LtBrain/MuBook/hardware/v.1/BIOS.kicad_sch

## KiCad design hardware/v.1/BIOS.kicad_sch (2025-07-30)

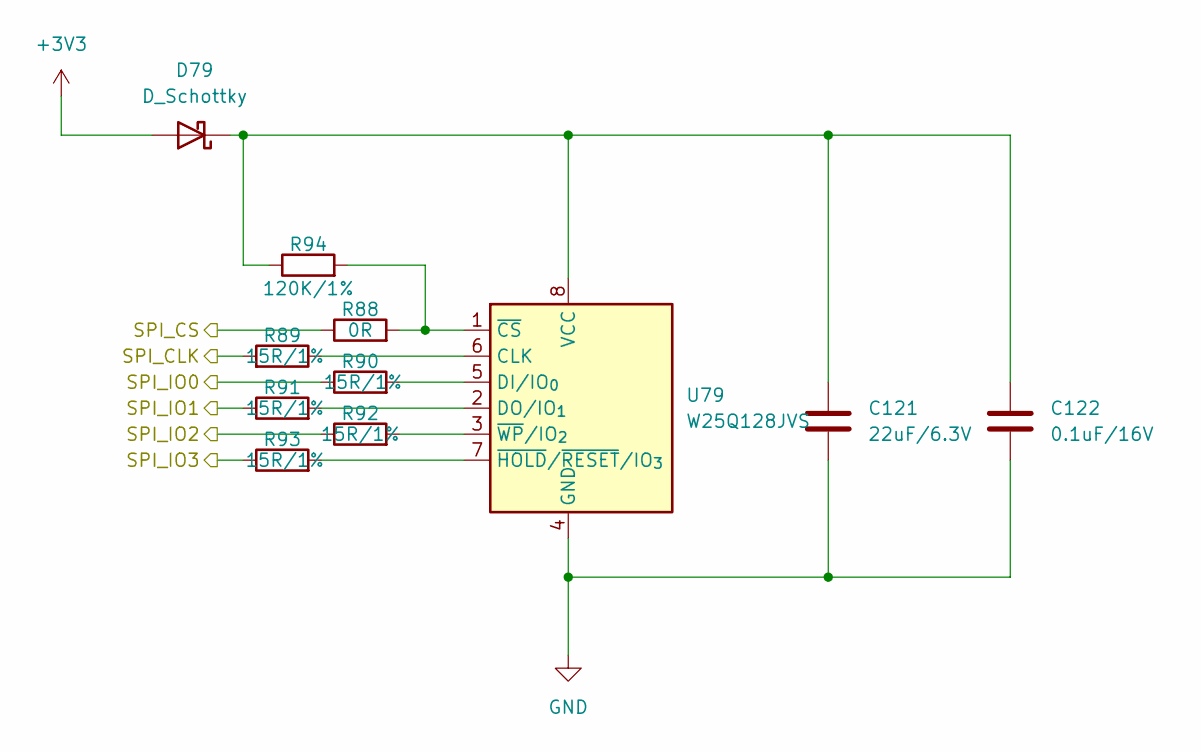
[picture p13: schematic BIOS.kicad_sch]

Parts:
C121: 22uF/6.3V; C_0402_1005Metric; Part# C105226; LCSC Part # C105226
C122: 0.1uF/16V; C_0402_1005Metric; Part# C83056; LCSC Part # C83056
D79: D_Schottky; D_SOD-923; Part# C239637; LCSC Part # C239637
R88: 0R; R_0402_1005Metric; Part# C325377; LCSC Part # C325377
R89, R90, R91, R92, R93: 15R/1%; R_0402_1005Metric; Part# C138052; LCSC Part # C138052
R94: 120K/1%; R_0402_1005Metric; Part# C93945; LCSC Part # C93945
U79: W25Q128JVS; SOIC-8_5.3x5.3mm_P1.27mm

Connections:
+3V3: D79.2 (A)
GND: C121.2, C122.2, U79.4 (GND)
unnamed: C121.1, C122.1, D79.1 (K), R94.1, U79.8 (VCC)
unnamed: R88.2, R94.2, U79.1 (~CS)
unnamed: R89.1, U79.6 (CLK)
unnamed: R90.2, U79.5 (DI/IO_{0})
unnamed: R91.2, U79.2 (DO/IO_{1})
unnamed: R92.2, U79.3 (~WP/IO_{2})
unnamed: R93.2, U79.7 (~HOLD/~RESET/IO_{3})
SPI_CLK: R89.2
SPI_CS: R88.1
SPI_IO0: R90.1
SPI_IO1: R91.1
SPI_IO2: R92.1
SPI_IO3: R93.1
