LtBrain/MuBook/hardware/v.1/GPIO.kicad_sch

## KiCad design hardware/v.1/GPIO.kicad_sch (2025-07-29)

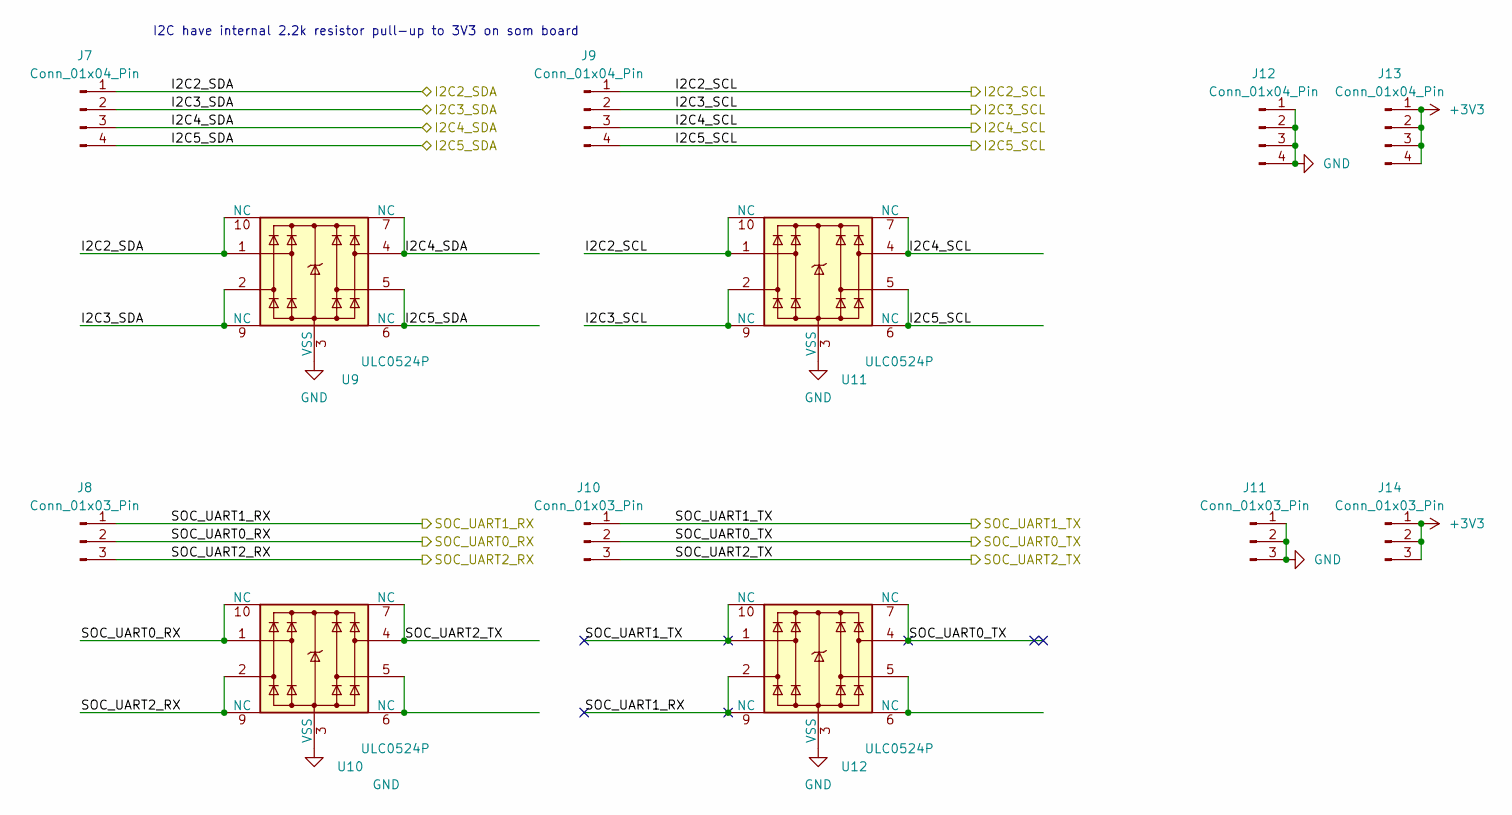
[picture p14: schematic GPIO.kicad_sch]

Parts:
J7, J9, J12, J13: Conn_01x04_Pin; PinHeader_1x04_P2.54mm_Vertical
J8, J10, J11, J14: Conn_01x03_Pin; PinHeader_1x03_P2.54mm_Vertical
U9, U10, U11, U12: ULC0524P; Diodes_UDFN-10_1.0x2.5mm_P0.5mm

Connections:
+3V3: J13.1, J13.2, J13.3, J13.4, J14.1, J14.2, J14.3
GND: J11.1, J11.2, J11.3, J12.1, J12.2, J12.3, J12.4, U9.3 (VSS), U9.8 (VSS), U10.3 (VSS), U10.8 (VSS), U11.3 (VSS), U11.8 (VSS), U12.3 (VSS), U12.8 (VSS)
I2C2_SCL: J9.1, U11.1, U11.10 (NC)
I2C2_SDA: J7.1, U9.1, U9.10 (NC)
I2C3_SCL: J9.2, U11.2, U11.9 (NC)
I2C3_SDA: J7.2, U9.2, U9.9 (NC)
I2C4_SCL: J9.3, U11.4, U11.7 (NC)
I2C4_SDA: J7.3, U9.4, U9.7 (NC)
I2C5_SCL: J9.4, U11.5, U11.6 (NC)
I2C5_SDA: J7.4, U9.5, U9.6 (NC)
unnamed: U10.5, U10.6 (NC)
unnamed: U12.5, U12.6 (NC)
SOC_UART0_RX: J8.2, U10.1, U10.10 (NC)
SOC_UART0_TX: J10.2, U12.4, U12.7 (NC)
SOC_UART1_RX: J8.1, U12.2, U12.9 (NC)
SOC_UART1_TX: J10.1, U12.1, U12.10 (NC)
SOC_UART2_RX: J8.3, U10.2, U10.9 (NC)
SOC_UART2_TX: J10.3, U10.4, U10.7 (NC)

Notes on the sheet:
I2C have internal 2.2k resistor pull-up to 3V3 on som board
