LtBrain/MuBook/hardware/v.1/Gigabit Ethernet.kicad_sch

## KiCad design hardware/v.1/Gigabit Ethernet.kicad_sch (2025-07-12)

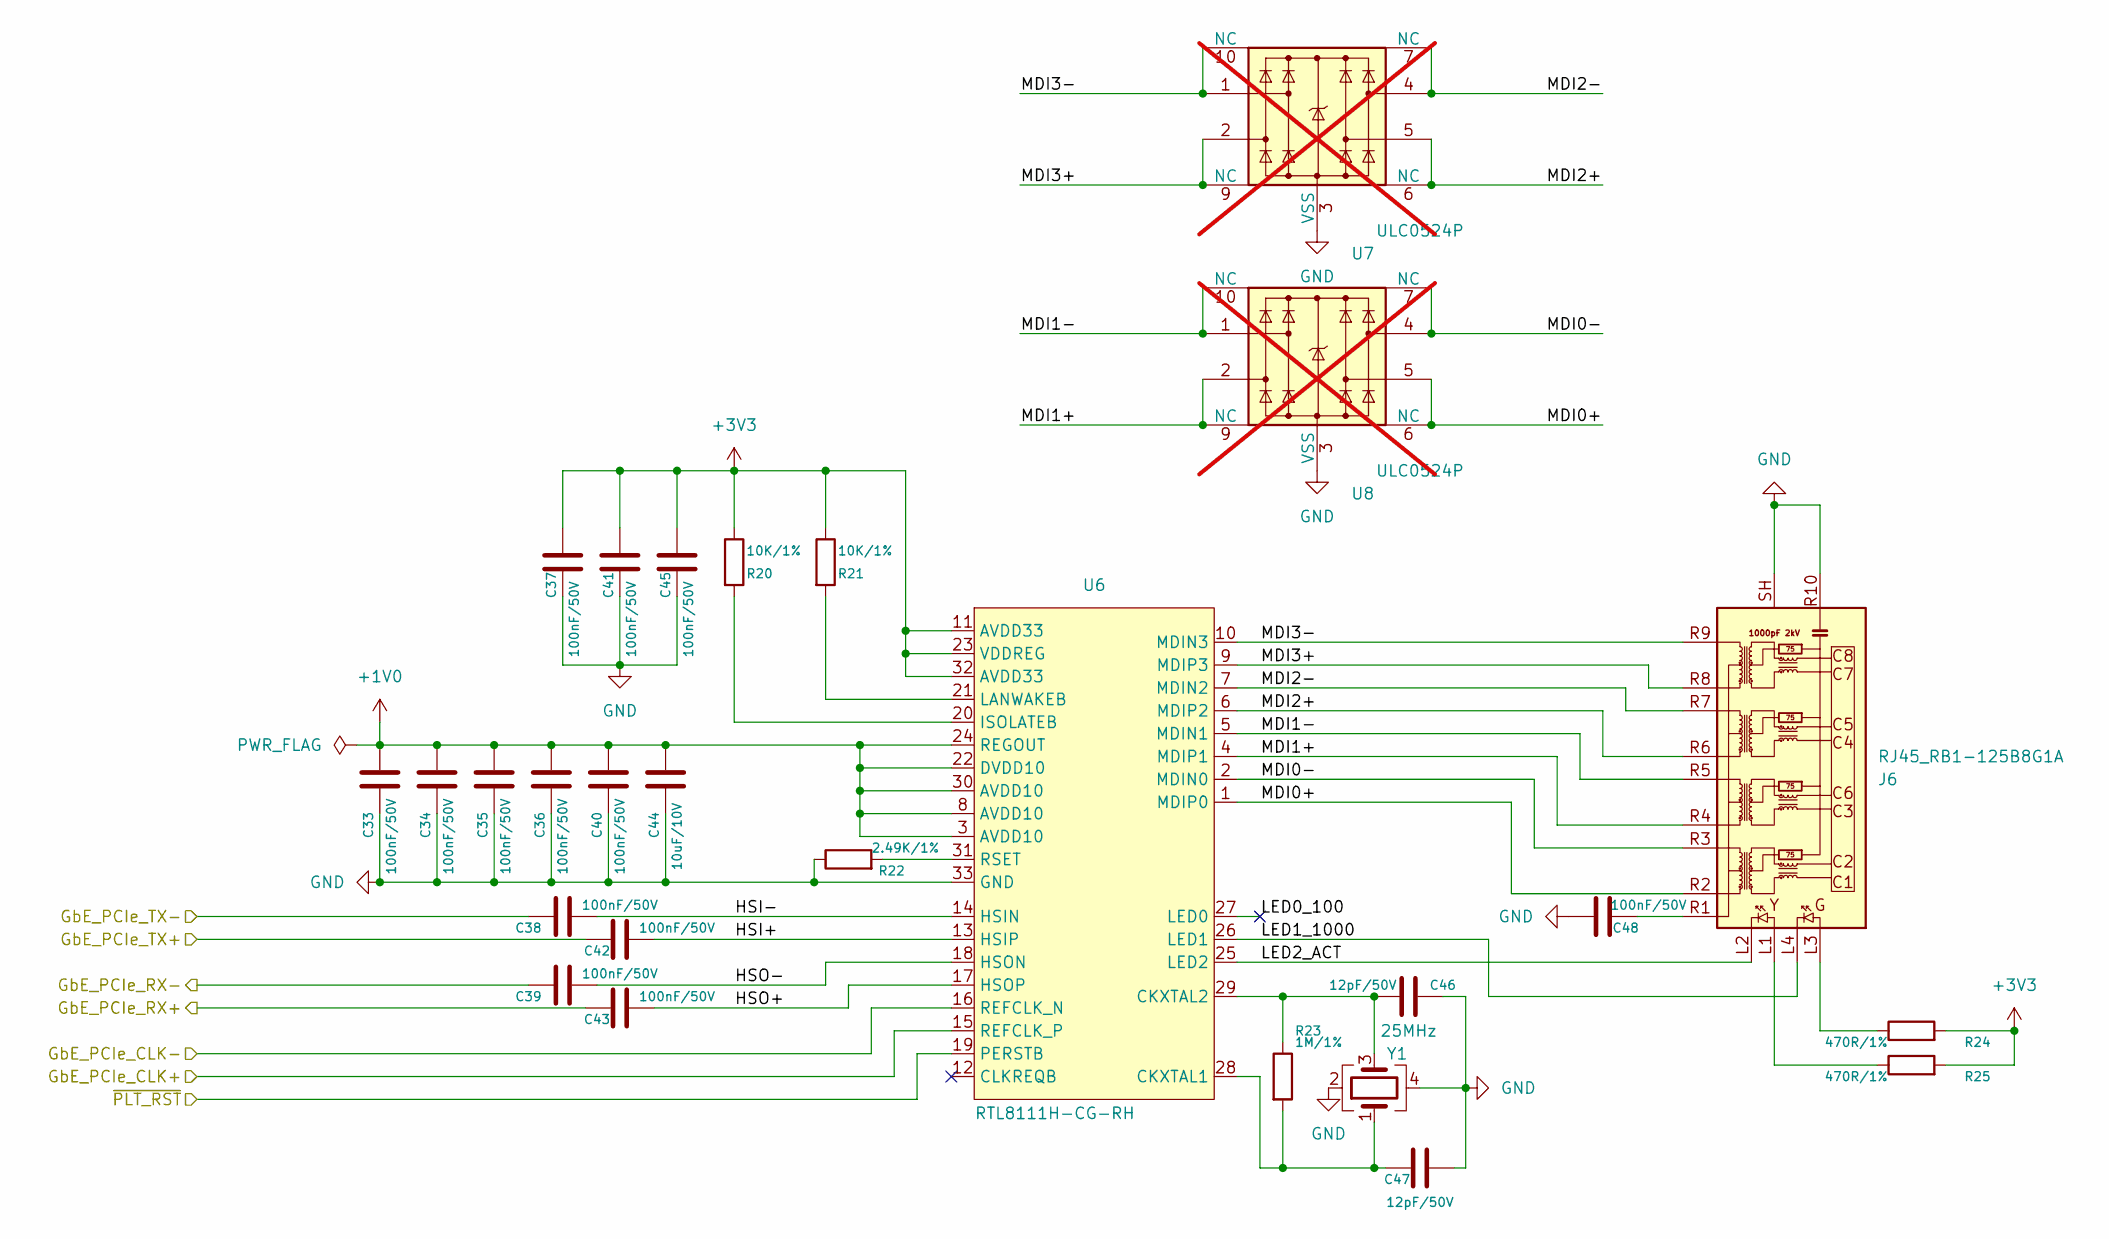
[picture p15: schematic Gigabit Ethernet.kicad_sch]

Parts:
C33, C34, C35, C36, C37, C38, C39, C40, C41, C42, C43, C45, C48: 100nF/50V; C_0402_1005Metric
C44: 10uF/10V; C_0402_1005Metric
C46, C47: 12pF/50V; C_0402_1005Metric
J6: RJ45_RB1-125B8G1A; RJ45_UDE_RB1-125B8G1A
R20, R21: 10K/1%; R_0402_1005Metric
R22: 2.49K/1%; R_0603_1608Metric
R23: 1M/1%; R_0402_1005Metric
R24, R25: 470R/1%; R_0402_1005Metric
U6: RTL8111H-CG-RH; QFN-32-1EP_4x4mm_P0.4mm_EP2.65x2.65mm
U7, U8: ULC0524P; Diodes_UDFN-10_1.0x2.5mm_P0.5mm; not fitted
Y1: 25MHz; Crystal_SMD_3225-4Pin_3.2x2.5mm

Connections:
+1V0: C33.2, C34.2, C35.2, C36.2, C40.2, C44.2, U6.3 (AVDD10), U6.8 (AVDD10), U6.22 (DVDD10), U6.24 (REGOUT), U6.30 (AVDD10)
+3V3: C37.2, C41.2, C45.2, R20.1, R21.1, R24.2, R25.2, U6.11 (AVDD33), U6.23 (VDDREG), U6.32 (AVDD33)
GND: C33.1, C34.1, C35.1, C36.1, C37.1, C40.1, C41.1, C44.1, C45.1, C46.1, C47.1, C48.2, J6.R10 (GND), J6.SH, R22.1, U6.33 (GND), U7.3 (VSS), U7.8 (VSS), U8.3 (VSS), U8.8 (VSS), Y1.2, Y1.4
GbE_PCIe_CLK+: U6.15 (REFCLK_P)
GbE_PCIe_CLK-: U6.16 (REFCLK_N)
GbE_PCIe_RX+: C43.2
GbE_PCIe_RX-: C39.2
GbE_PCIe_TX+: C42.2
GbE_PCIe_TX-: C38.2
HSI+: C42.1, U6.13 (HSIP)
HSI-: C38.1, U6.14 (HSIN)
HSO+: C43.1, U6.17 (HSOP)
HSO-: C39.1, U6.18 (HSON)
LED0_100: U6.27 (LED0)
LED1_1000: J6.L4, U6.26 (LED1)
LED2_ACT: J6.L2, U6.25 (LED2)
MDI0+: J6.R2 (TD1+), U6.1 (MDIP0), U8.5, U8.6 (NC)
MDI0-: J6.R3 (TD1-), U6.2 (MDIN0), U8.4, U8.7 (NC)
MDI1+: J6.R4 (TD2+), U6.4 (MDIP1), U8.2, U8.9 (NC)
MDI1-: J6.R5 (TD2-), U6.5 (MDIN1), U8.1, U8.10 (NC)
MDI2+: J6.R6 (TD3+), U6.6 (MDIP2), U7.5, U7.6 (NC)
MDI2-: J6.R7 (TD3-), U6.7 (MDIN2), U7.4, U7.7 (NC)
MDI3+: J6.R8 (TD4+), U6.9 (MDIP3), U7.2, U7.9 (NC)
MDI3-: J6.R9 (TD4-), U6.10 (MDIN3), U7.1, U7.10 (NC)
unnamed: C46.2, R23.1, U6.29 (CKXTAL2), Y1.3
unnamed: C47.2, R23.2, U6.28 (CKXTAL1), Y1.1
unnamed: C48.1, J6.R1 (CT)
unnamed: J6.L1, R25.1
unnamed: J6.L3, R24.1
unnamed: R20.2, U6.20 (ISOLATEB)
unnamed: R21.2, U6.21 (LANWAKEB)
unnamed: R22.2, U6.31 (RSET)
~PLT_RST: U6.19 (PERSTB)
