LtBrain/MuBook/hardware/v.1/HDMI.kicad_sch

## KiCad design hardware/v.1/HDMI.kicad_sch (2025-07-12)

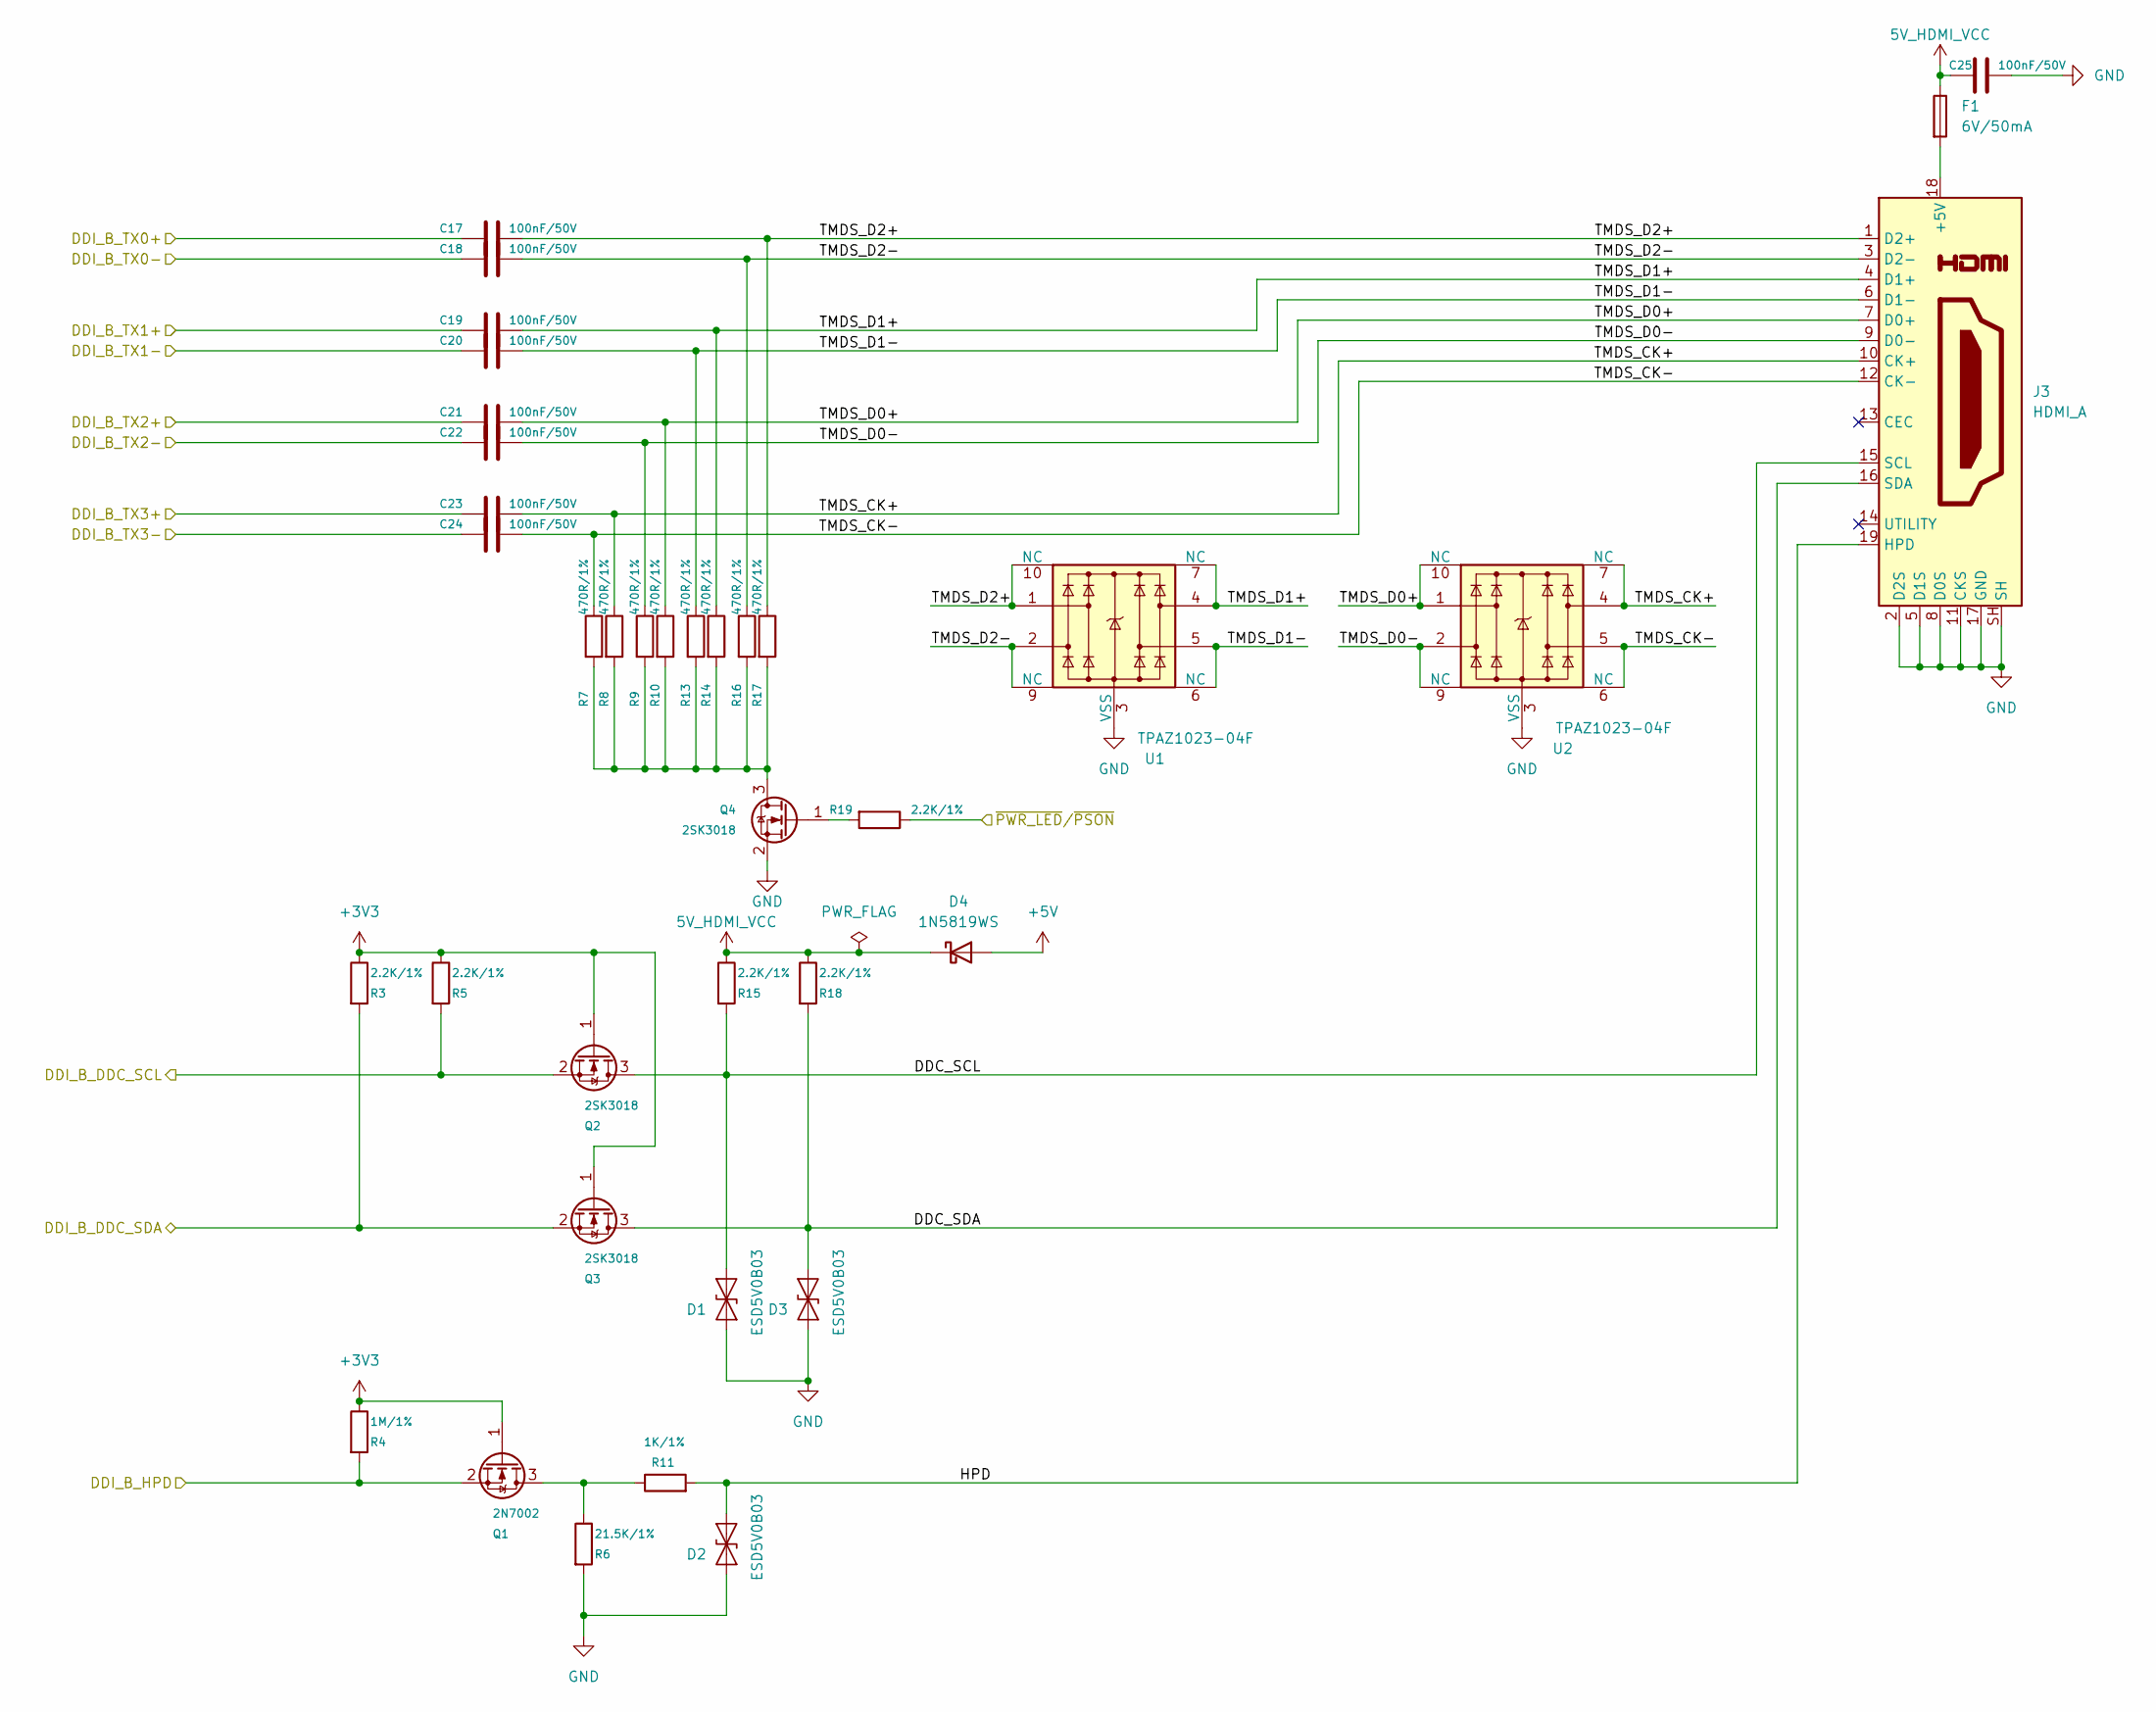
[picture p16: schematic HDMI.kicad_sch]

Parts:
C17, C18, C19, C20, C21, C22, C23, C24, C25: 100nF/50V; C_0402_1005Metric
D1, D2, D3: ESD5V0B03; D_0402_1005Metric
D4: 1N5819WS; D_SOD-323
F1: 6V/50mA; R_0603_1608Metric
J3: HDMI_A; HDMI_A_Molex_208658-1001_Horizontal
Q1: 2N7002; SOT-23
Q2, Q3, Q4: 2SK3018; SOT-23
R3, R5, R15, R18, R19: 2.2K/1%; R_0402_1005Metric
R4: 1M/1%; R_0402_1005Metric
R6: 21.5K/1%; R_0402_1005Metric
R7, R8, R9, R10, R13, R14, R16, R17: 470R/1%; R_0402_1005Metric
R11: 1K/1%; R_0402_1005Metric
U1, U2: TPAZ1023-04F; Diodes_UDFN-10_1.0x2.5mm_P0.5mm

Connections:
5V_HDMI_VCC: C25.1, D4.1 (K), F1.1, R15.1, R18.1
+3V3: Q1.1 (G), Q2.1 (G), Q3.1 (G), R3.1, R4.1, R5.1
+5V: D4.2 (A)
DDC_SCL: D1.2 (A2), J3.15 (SCL), Q2.3 (D), R15.2
DDC_SDA: D3.2 (A2), J3.16 (SDA), Q3.3 (D), R18.2
DDI_B_DDC_SCL: Q2.2 (S), R5.2
DDI_B_DDC_SDA: Q3.2 (S), R3.2
DDI_B_HPD: Q1.2 (S), R4.2
DDI_B_TX0+: C17.1
DDI_B_TX0-: C18.1
DDI_B_TX1+: C19.1
DDI_B_TX1-: C20.1
DDI_B_TX2+: C21.1
DDI_B_TX2-: C22.1
DDI_B_TX3+: C23.1
DDI_B_TX3-: C24.1
GND: C25.2, D1.1 (A1), D2.1 (A1), D3.1 (A1), J3.2 (D2S), J3.5 (D1S), J3.8 (D0S), J3.11 (CKS), J3.17 (GND), J3.SH, Q4.2 (S), R6.2, U1.3 (VSS), U1.8 (VSS), U2.3 (VSS), U2.8 (VSS)
HPD: D2.2 (A2), J3.19 (HPD), R11.2
unnamed: F1.2, J3.18 (+5V)
unnamed: Q1.3 (D), R6.1, R11.1
unnamed: Q4.1 (G), R19.2
unnamed: Q4.3 (D), R7.2, R8.2, R9.2, R10.2, R13.2, R14.2, R16.2, R17.2
TMDS_CK+: C23.2, J3.10 (CK+), R8.1, U2.4, U2.7 (NC)
TMDS_CK-: C24.2, J3.12 (CK-), R7.1, U2.5, U2.6 (NC)
TMDS_D0+: C21.2, J3.7 (D0+), R10.1, U2.1, U2.10 (NC)
TMDS_D0-: C22.2, J3.9 (D0-), R9.1, U2.2, U2.9 (NC)
TMDS_D1+: C19.2, J3.4 (D1+), R14.1, U1.4, U1.7 (NC)
TMDS_D1-: C20.2, J3.6 (D1-), R13.1, U1.5, U1.6 (NC)
TMDS_D2+: C17.2, J3.1 (D2+), R17.1, U1.1, U1.10 (NC)
TMDS_D2-: C18.2, J3.3 (D2-), R16.1, U1.2, U1.9 (NC)
~PWR_LED/~PSON: R19.1
