LtBrain/MuBook/hardware/v.1/LattePanda Module.kicad_sch

## KiCad design hardware/v.1/LattePanda Module.kicad_sch (2025-08-01)

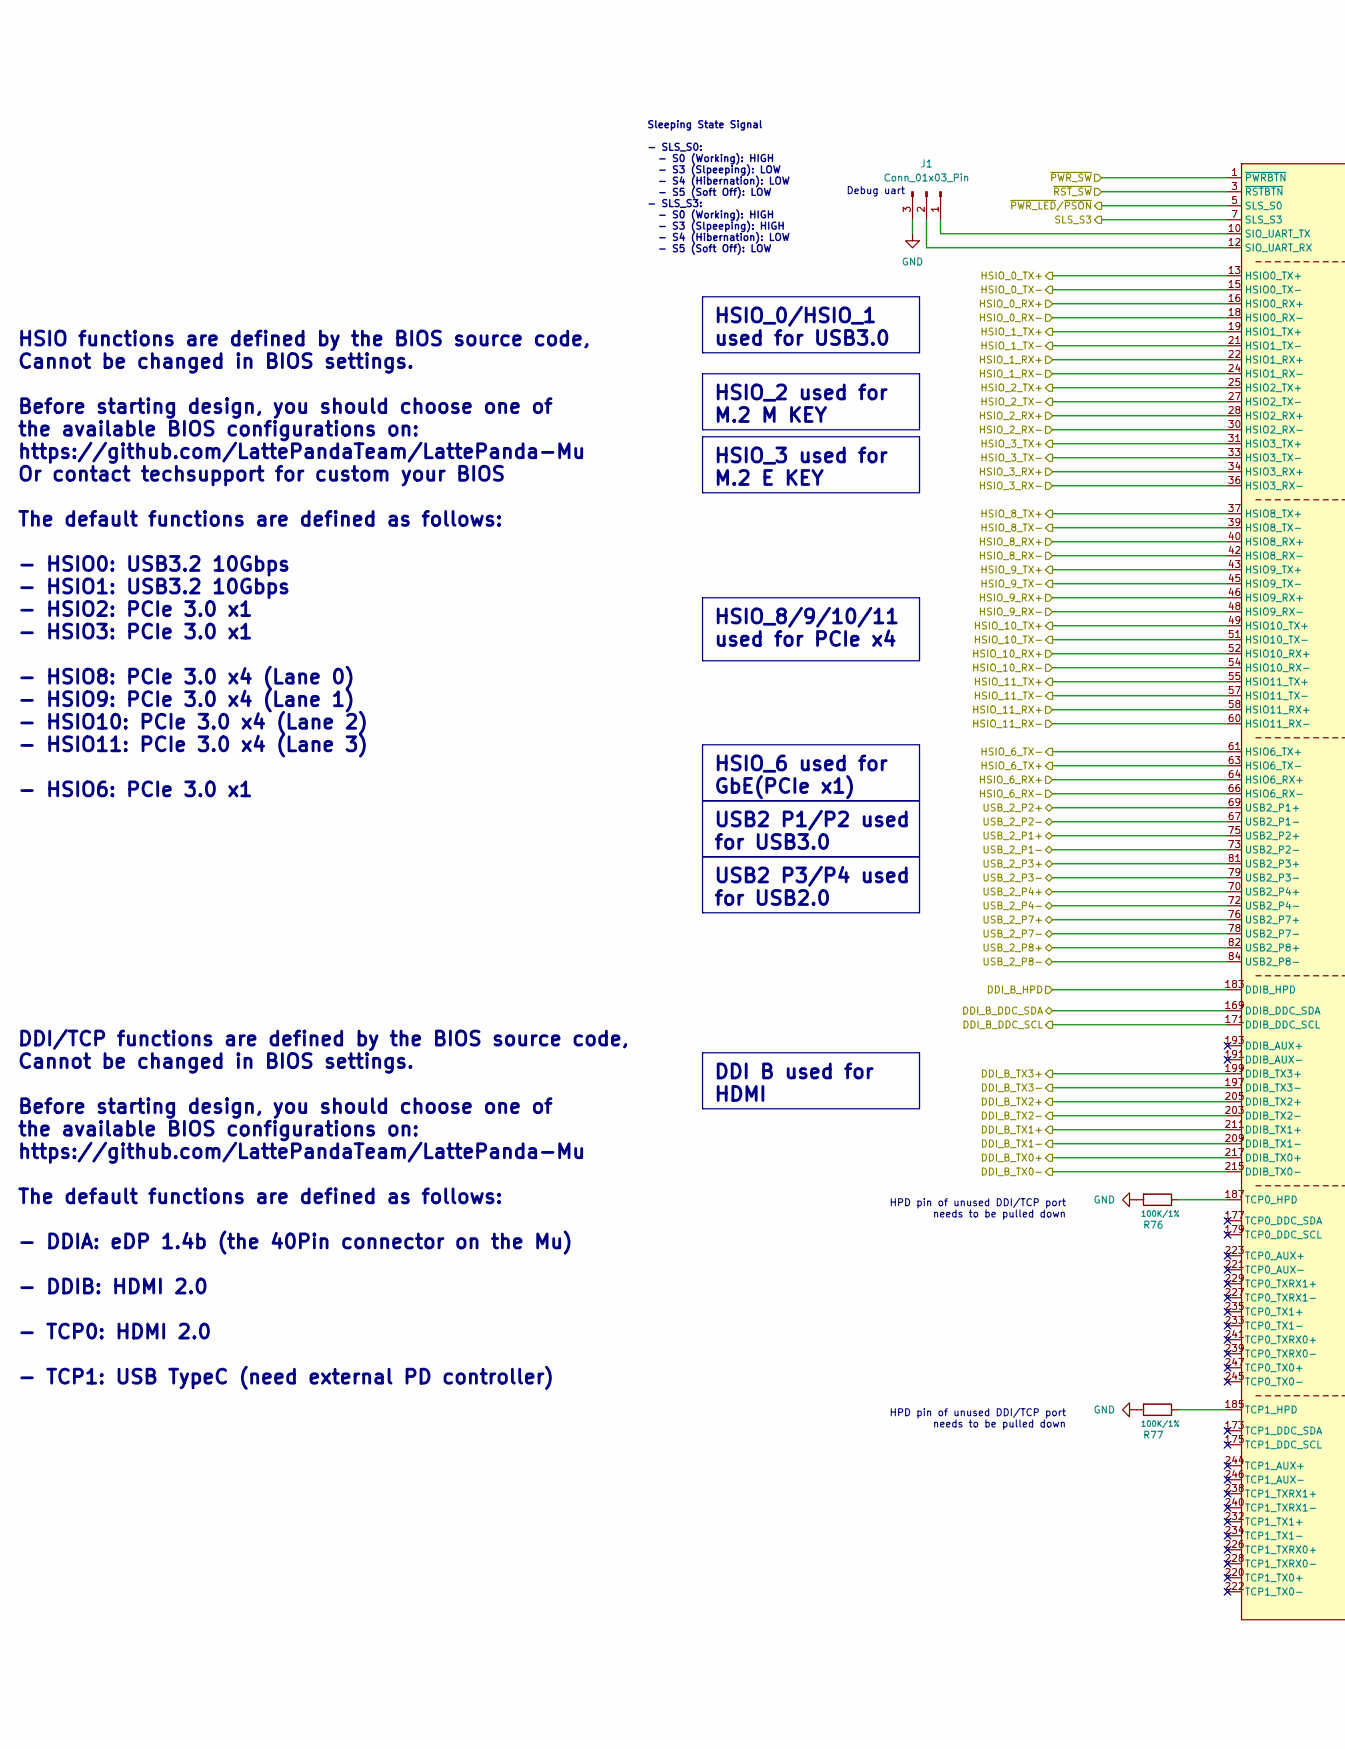
[picture p17: schematic LattePanda Module.kicad_sch, part in row 1, column 1]

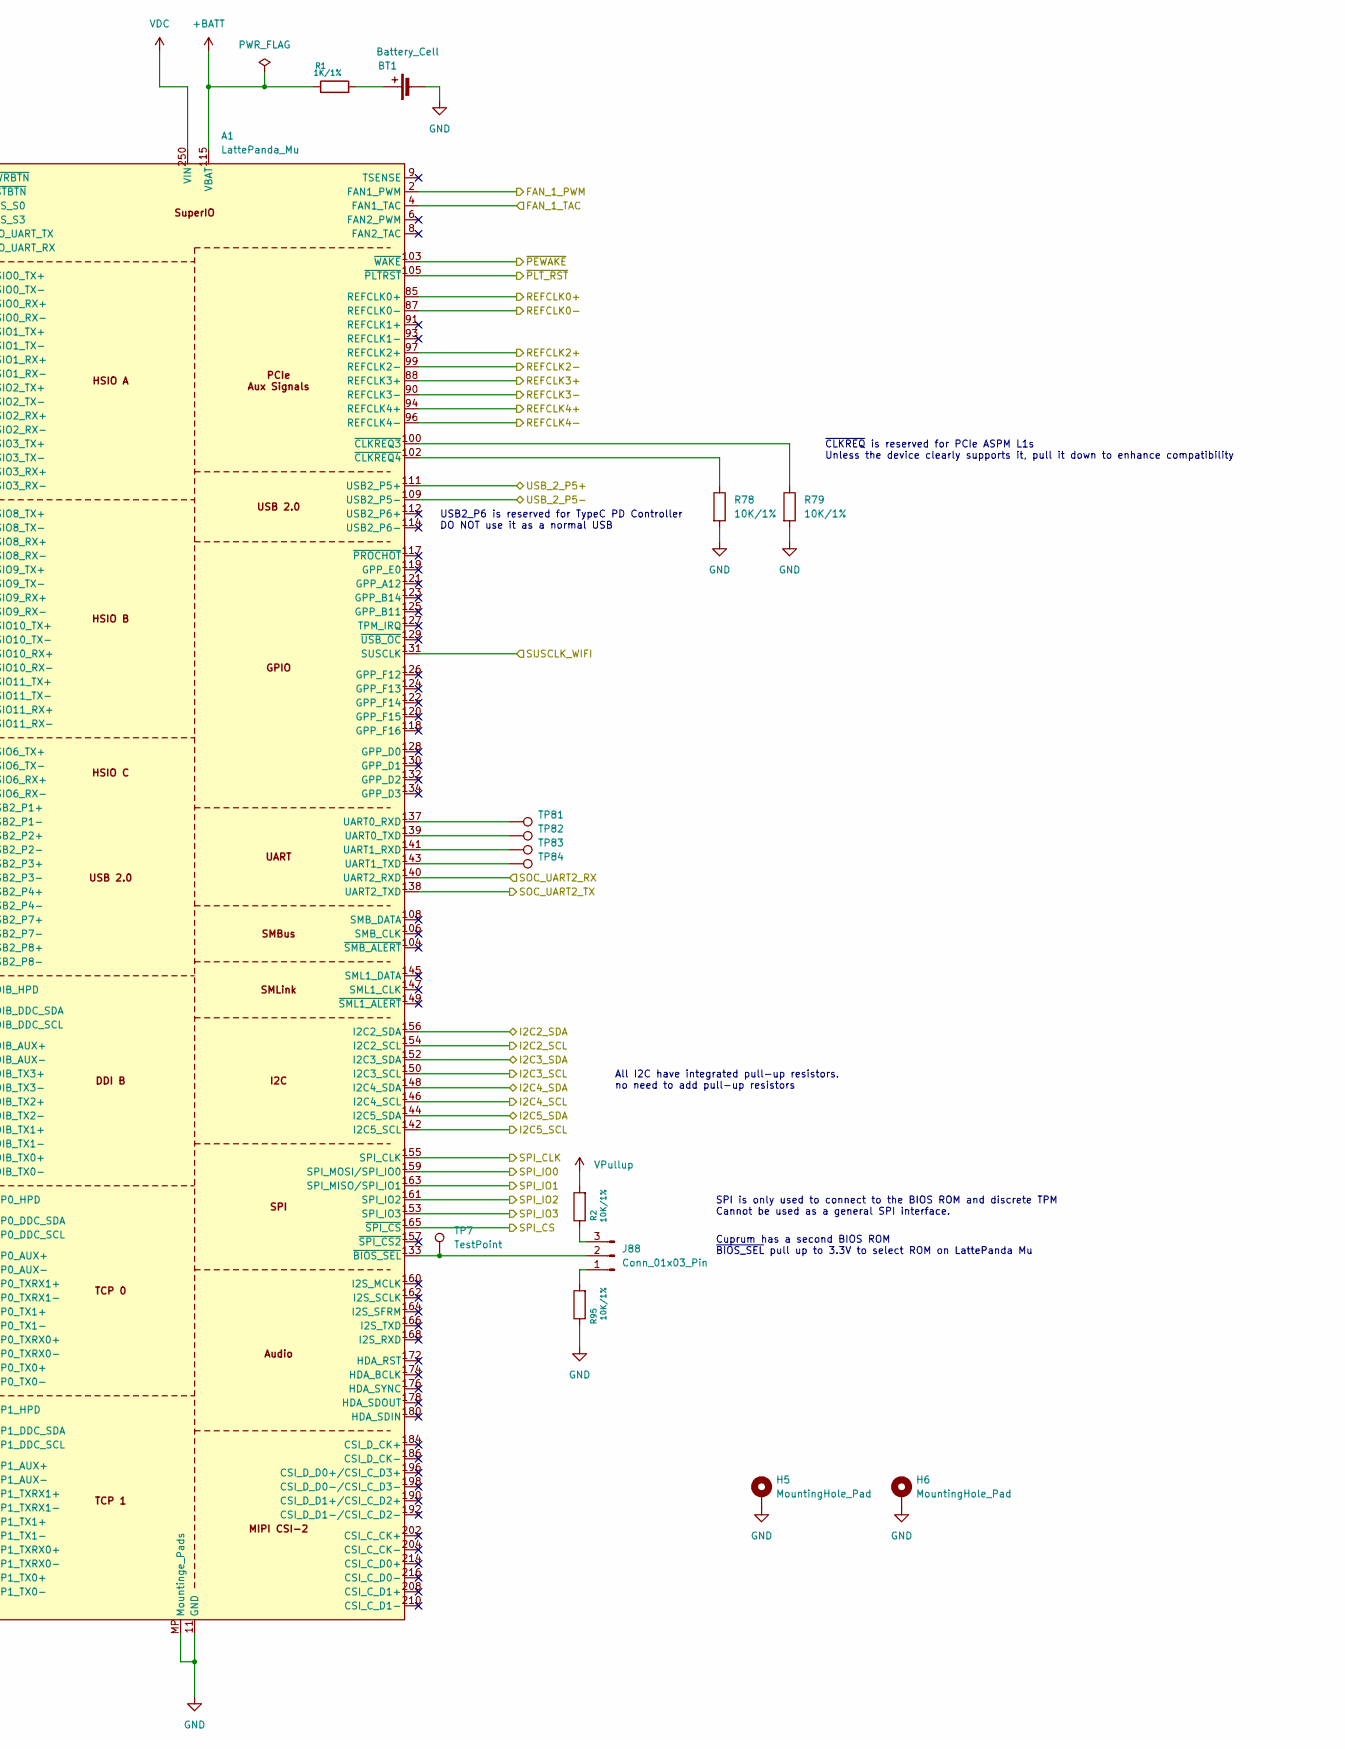
[picture p18: schematic LattePanda Module.kicad_sch, part in row 1, column 2]

Parts:
A1: LattePanda_Mu; LattePanda_Module_H8.0mm_Horizontal
BT1: Battery_Cell; Battery_Holder_CR1220_S8411-45R
H5, H6: MountingHole_Pad; MountingHole_2.2mm_M2_DIN965_Pad
J1: Conn_01x03_Pin; PinHeader_1x03_P2.54mm_Vertical
J88: Conn_01x03_Pin; PinHeader_1x03_P2.54mm_Vertical; MPN PZ2.54-1*3
R1: 1K/1%; R_0402_1005Metric
R2, R95: 10K/1%; R_0402_1005Metric; Part# C60490; LCSC Part # C60490
R76, R77: 100K/1%; R_0402_1005Metric
R78, R79: 10K/1%; R_0402_1005Metric
TP7: TestPoint; TestPoint_Pad_D1.5mm
TP81, TP82, TP83, TP84: TestPoint; TestPoint_Pad_D1.0mm

Connections:
+BATT: A1.115 (VBAT), R1.1
DDI_B_DDC_SCL: A1.171 (DDIB_DDC_SCL)
DDI_B_DDC_SDA: A1.169 (DDIB_DDC_SDA)
DDI_B_HPD: A1.183 (DDIB_HPD)
DDI_B_TX0+: A1.217 (DDIB_TX0+)
DDI_B_TX0-: A1.215 (DDIB_TX0-)
DDI_B_TX1+: A1.211 (DDIB_TX1+)
DDI_B_TX1-: A1.209 (DDIB_TX1-)
DDI_B_TX2+: A1.205 (DDIB_TX2+)
DDI_B_TX2-: A1.203 (DDIB_TX2-)
DDI_B_TX3+: A1.199 (DDIB_TX3+)
DDI_B_TX3-: A1.197 (DDIB_TX3-)
FAN_1_PWM: A1.2 (FAN1_PWM)
FAN_1_TAC: A1.4 (FAN1_TAC)
GND: A1.11 (GND), A1.14 (GND), A1.17 (GND), A1.20 (GND), A1.23 (GND), A1.26 (GND), A1.29 (GND), A1.32 (GND), A1.35 (GND), A1.38 (GND), A1.41 (GND), A1.44 (GND), A1.47 (GND), A1.50 (GND), A1.53 (GND), A1.56 (GND), A1.59 (GND), A1.62 (GND), A1.65 (GND), A1.68 (GND), A1.71 (GND), A1.74 (GND), A1.77 (GND), A1.80 (GND), A1.83 (GND), A1.86 (GND), A1.89 (GND), A1.92 (GND), A1.95 (GND), A1.98 (GND), A1.101 (GND), A1.107 (GND), A1.110 (GND), A1.113 (GND), A1.116 (GND), A1.135 (GND), A1.136 (GND), A1.151 (GND), A1.158 (GND), A1.167 (GND), A1.170 (GND), A1.181 (GND), A1.182 (GND), A1.188 (GND), A1.189 (GND), A1.194 (GND), A1.195 (GND), A1.200 (GND), A1.201 (GND), A1.206 (GND), A1.207 (GND), A1.212 (GND), A1.213 (GND), A1.218 (GND), A1.219 (GND), A1.224 (GND), A1.225 (GND), A1.230 (GND), A1.231 (GND), A1.236 (GND), A1.237 (GND), A1.242 (GND), A1.243 (GND), A1.248 (GND), A1.249 (GND), A1.MP (Mountinge_Pads), BT1.2 (-), H5.1, H6.1, J1.3, R76.2, R77.2, R78.2, R79.2, R95.1
HSIO_0_RX+: A1.16 (HSIO0_RX+)
HSIO_0_RX-: A1.18 (HSIO0_RX-)
HSIO_0_TX+: A1.13 (HSIO0_TX+)
HSIO_0_TX-: A1.15 (HSIO0_TX-)
HSIO_1_RX+: A1.22 (HSIO1_RX+)
HSIO_1_RX-: A1.24 (HSIO1_RX-)
HSIO_1_TX+: A1.19 (HSIO1_TX+)
HSIO_1_TX-: A1.21 (HSIO1_TX-)
HSIO_2_RX+: A1.28 (HSIO2_RX+)
HSIO_2_RX-: A1.30 (HSIO2_RX-)
HSIO_2_TX+: A1.25 (HSIO2_TX+)
HSIO_2_TX-: A1.27 (HSIO2_TX-)
HSIO_3_RX+: A1.34 (HSIO3_RX+)
HSIO_3_RX-: A1.36 (HSIO3_RX-)
HSIO_3_TX+: A1.31 (HSIO3_TX+)
HSIO_3_TX-: A1.33 (HSIO3_TX-)
HSIO_6_RX+: A1.64 (HSIO6_RX+)
HSIO_6_RX-: A1.66 (HSIO6_RX-)
HSIO_6_TX+: A1.63 (HSIO6_TX-)
HSIO_6_TX-: A1.61 (HSIO6_TX+)
HSIO_8_RX+: A1.40 (HSIO8_RX+)
HSIO_8_RX-: A1.42 (HSIO8_RX-)
HSIO_8_TX+: A1.37 (HSIO8_TX+)
HSIO_8_TX-: A1.39 (HSIO8_TX-)
HSIO_9_RX+: A1.46 (HSIO9_RX+)
HSIO_9_RX-: A1.48 (HSIO9_RX-)
HSIO_9_TX+: A1.43 (HSIO9_TX+)
HSIO_9_TX-: A1.45 (HSIO9_TX-)
HSIO_10_RX+: A1.52 (HSIO10_RX+)
HSIO_10_RX-: A1.54 (HSIO10_RX-)
HSIO_10_TX+: A1.49 (HSIO10_TX+)
HSIO_10_TX-: A1.51 (HSIO10_TX-)
HSIO_11_RX+: A1.58 (HSIO11_RX+)
HSIO_11_RX-: A1.60 (HSIO11_RX-)
HSIO_11_TX+: A1.55 (HSIO11_TX+)
HSIO_11_TX-: A1.57 (HSIO11_TX-)
I2C2_SCL: A1.154 (I2C2_SCL)
I2C2_SDA: A1.156 (I2C2_SDA)
I2C3_SCL: A1.150 (I2C3_SCL)
I2C3_SDA: A1.152 (I2C3_SDA)
I2C4_SCL: A1.146 (I2C4_SCL)
I2C4_SDA: A1.148 (I2C4_SDA)
I2C5_SCL: A1.142 (I2C5_SCL)
I2C5_SDA: A1.144 (I2C5_SDA)
unnamed: A1.10 (SIO_UART_TX), J1.1
unnamed: A1.12 (SIO_UART_RX), J1.2
unnamed: A1.100 (~CLKREQ3), R79.1
unnamed: A1.102 (~CLKREQ4), R78.1
unnamed: A1.133 (~BIOS_SEL), J88.2, TP7.1
unnamed: A1.137 (UART0_RXD), TP81.1
unnamed: A1.139 (UART0_TXD), TP82.1
unnamed: A1.141 (UART1_RXD), TP83.1
unnamed: A1.143 (UART1_TXD), TP84.1
unnamed: A1.185 (TCP1_HPD), R77.1
unnamed: A1.187 (TCP0_HPD), R76.1
unnamed: BT1.1 (+), R1.2
unnamed: J88.1, R95.2
unnamed: J88.3, R2.1
REFCLK0+: A1.85 (REFCLK0+)
REFCLK0-: A1.87 (REFCLK0-)
REFCLK2+: A1.97 (REFCLK2+)
REFCLK2-: A1.99 (REFCLK2-)
REFCLK3+: A1.88 (REFCLK3+)
REFCLK3-: A1.90 (REFCLK3-)
REFCLK4+: A1.94 (REFCLK4+)
REFCLK4-: A1.96 (REFCLK4-)
SLS_S3: A1.7 (SLS_S3)
SOC_UART2_RX: A1.140 (UART2_RXD)
SOC_UART2_TX: A1.138 (UART2_TXD)
SPI_CLK: A1.155 (SPI_CLK)
SPI_CS: A1.165 (~SPI_CS)
SPI_IO0: A1.159 (SPI_MOSI/SPI_IO0)
SPI_IO1: A1.163 (SPI_MISO/SPI_IO1)
SPI_IO2: A1.161 (SPI_IO2)
SPI_IO3: A1.153 (SPI_IO3)
SUSCLK_WIFI: A1.131 (SUSCLK)
USB_2_P1+: A1.75 (USB2_P2+)
USB_2_P1-: A1.73 (USB2_P2-)
USB_2_P2+: A1.69 (USB2_P1+)
USB_2_P2-: A1.67 (USB2_P1-)
USB_2_P3+: A1.81 (USB2_P3+)
USB_2_P3-: A1.79 (USB2_P3-)
USB_2_P4+: A1.70 (USB2_P4+)
USB_2_P4-: A1.72 (USB2_P4-)
USB_2_P5+: A1.111 (USB2_P5+)
USB_2_P5-: A1.109 (USB2_P5-)
USB_2_P7+: A1.76 (USB2_P7+)
USB_2_P7-: A1.78 (USB2_P7-)
USB_2_P8+: A1.82 (USB2_P8+)
USB_2_P8-: A1.84 (USB2_P8-)
VDC: A1.250 (VIN), A1.251 (VIN), A1.252 (VIN), A1.253 (VIN), A1.254 (VIN), A1.255 (VIN), A1.256 (VIN), A1.257 (VIN), A1.258 (VIN), A1.259 (VIN), A1.260 (VIN)
VPullup: R2.2
~PEWAKE: A1.103 (~WAKE)
~PLT_RST: A1.105 (~PLTRST)
~PWR_LED/~PSON: A1.5 (SLS_S0)
~PWR_SW: A1.1 (~PWRBTN)
~RST_SW: A1.3 (~RSTBTN)

Notes on the sheet:
HSIO functions are defined by the BIOS source code, Cannot be changed in BIOS settings. Before starting design, you should choose one of the available BIOS configurations on: https://github.com/LattePandaTeam/LattePanda-Mu Or contact techsupport for custom your BIOS The default functions are define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
HPD pin of unused DDI/TCP port needs to be pulled down
Cuprum has a second BIOS ROM ~{BIOS_SEL} pull up to 3.3V to select ROM on LattePanda Mu
DDI/TCP functions are defined by the BIOS source code, Cannot be changed in BIOS settings. Before starting design, you should choose one of the available BIOS configurations on: https://github.com/LattePandaTeam/LattePanda-Mu The default functions are defined as follows: - DDIA: eDP 1.4b (the 40Pin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
Sleeping State Signal - SLS_S0: - S0 (Working): HIGH - S3 (Slpeeping): LOW - S4 (Hibernation): LOW - S5 (Soft Off): LOW - SLS_S3: - S0 (Working): HIGH - S3 (Slpeeping): HIGH - S4 (Hibernation): LOW - S5 (Soft Off): LOW
USB2_P6 is reserved for TypeC PD Controller DO NOT use it as a normal USB
SPI is only used to connect to the BIOS ROM and discrete TPM Cannot be used as a general SPI interface.
All I2C have integrated pull-up resistors. no need to add pull-up resistors
Debug uart
~{CLKREQ} is reserved for PCIe ASPM L1s Unless the device clearly supports it, pull it down to enhance compatibility
HSIO_0/HSIO_1 used for USB3.0
HSIO_2 used for M.2 M KEY
HSIO_6 used for GbE(PCIe x1)
USB2 P3/P4 used for USB2.0
DDI B used for HDMI
HSIO_3 used for M.2 E KEY
HSIO_8/9/10/11 used for PCIe x4
USB2 P1/P2 used for USB3.0
