LtBrain/MuBook/hardware/v.1/M.2 E&M Key.kicad_sch

## KiCad design hardware/v.1/M.2 E&M Key.kicad_sch (2025-07-12)

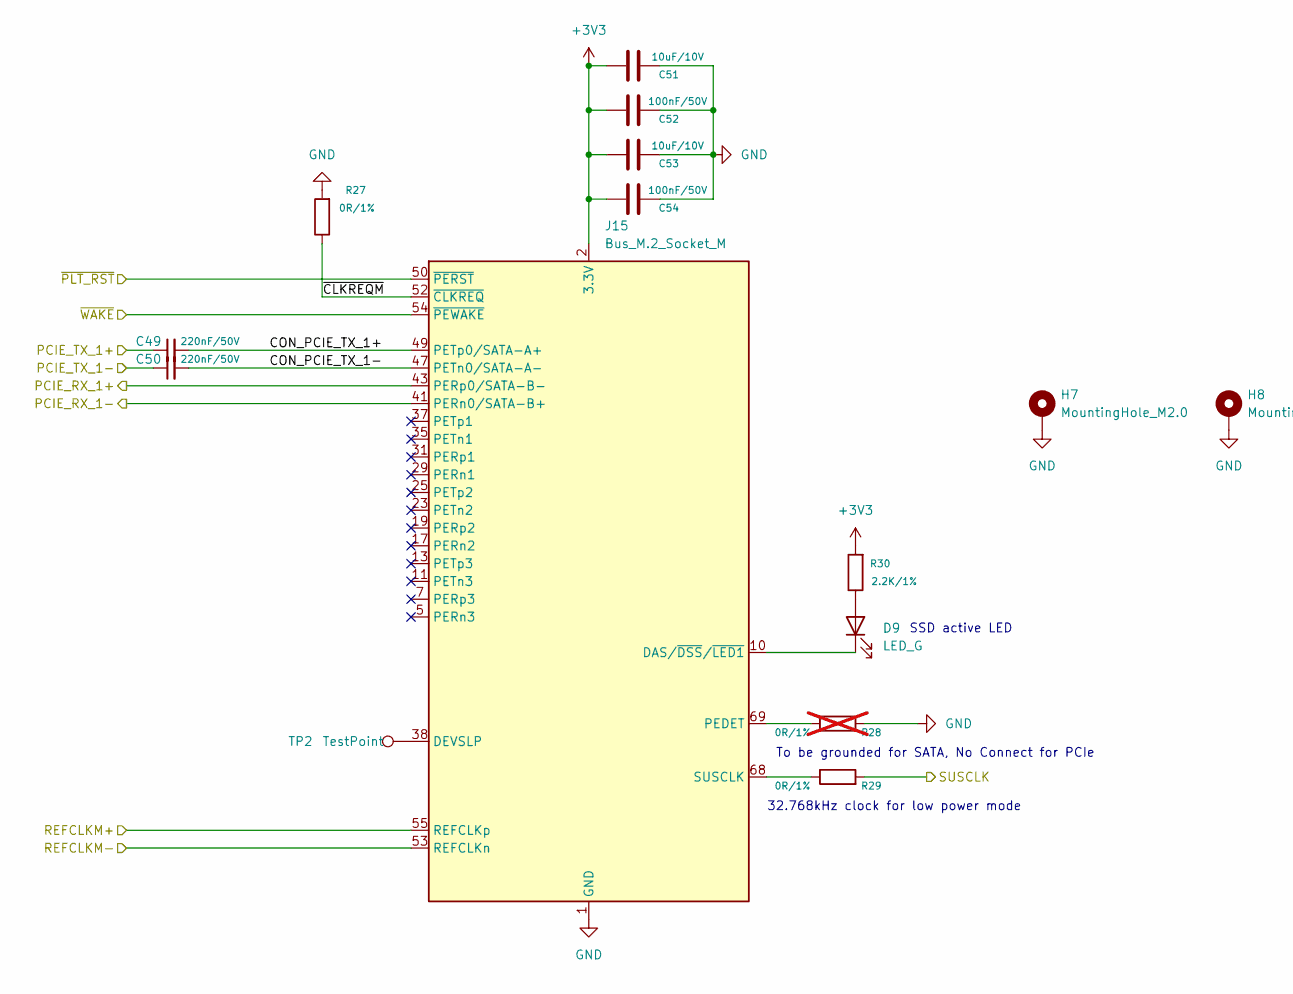
[picture p19: schematic M.2 E&M Key.kicad_sch, part in row 1, column 1]

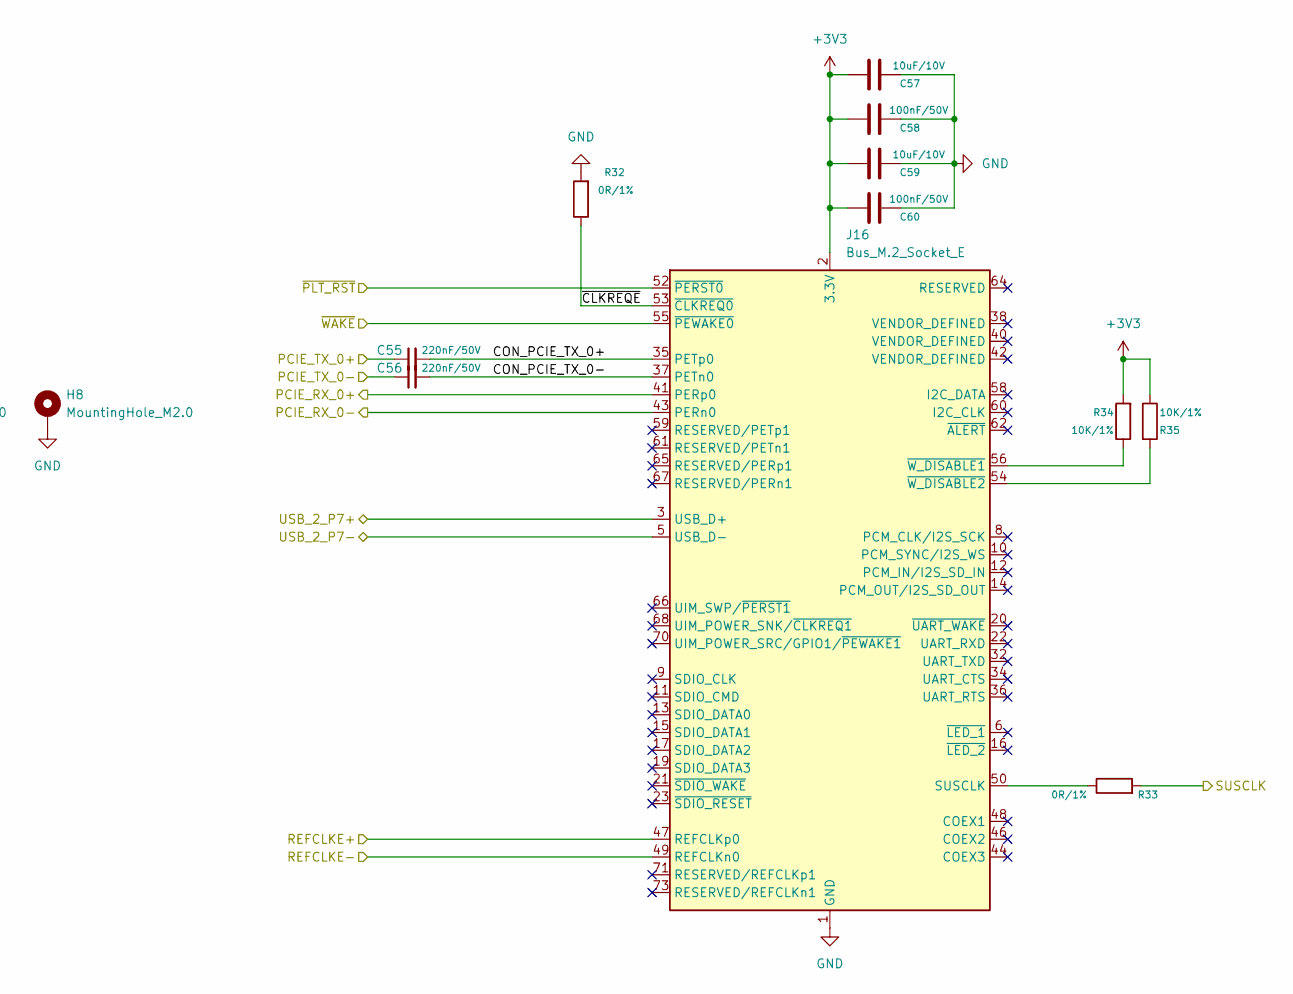
[picture p20: schematic M.2 E&M Key.kicad_sch, part in row 1, column 2]

Parts:
C49, C50, C55, C56: 220nF/50V; C_0402_1005Metric
C51, C53, C57, C59: 10uF/10V; C_0402_1005Metric
C52, C54, C58, C60: 100nF/50V; C_0402_1005Metric
D9: LED_G; LED_0603_1608Metric
H7, H8: MountingHole_M2.0; MountingHole_2.75mm_M2_4.4mm_Pad_TopOnly
J15: Bus_M.2_Socket_M; PCIe_M.2_Connectors_P=0.5mm_H=4.2mm_KeyM
J16: Bus_M.2_Socket_E; PCIe_M.2_Connectors_P=0.5mm_H=4.2mm_KeyE
R27, R29, R32, R33: 0R/1%; R_0402_1005Metric
R28: 0R/1%; R_0402_1005Metric; not fitted
R30: 2.2K/1%; R_0402_1005Metric
R34, R35: 10K/1%; R_0402_1005Metric
TP2: TestPoint; TestPoint_Pad_D1.5mm

Connections:
+3V3: C51.2, C52.2, C53.2, C54.2, C57.2, C58.2, C59.2, C60.2, J15.2 (3.3V), J15.4 (3.3V), J15.12 (3.3V), J15.14 (3.3V), J15.16 (3.3V), J15.18 (3.3V), J15.70 (3.3V), J15.72 (3.3V), J15.74 (3.3V), J16.2 (3.3V), J16.4 (3.3V), J16.72 (3.3V), J16.74 (3.3V), R30.2, R34.2, R35.1
CON_PCIE_TX_0+: C55.2, J16.35 (PETp0)
CON_PCIE_TX_0-: C56.2, J16.37 (PETn0)
CON_PCIE_TX_1+: C49.2, J15.49 (PETp0/SATA-A+)
CON_PCIE_TX_1-: C50.2, J15.47 (PETn0/SATA-A-)
GND: C51.1, C52.1, C53.1, C54.1, C57.1, C58.1, C59.1, C60.1, H7.1, H8.1, J15.1 (GND), J15.3 (GND), J15.9 (GND), J15.15 (GND), J15.21 (GND), J15.27 (GND), J15.33 (GND), J15.39 (GND), J15.45 (GND), J15.51 (GND), J15.57 (GND), J15.71 (GND), J15.73 (GND), J15.75 (GND), J15.MP1, J15.MP2, J16.1 (GND), J16.7 (GND), J16.18 (GND), J16.33 (GND), J16.39 (GND), J16.45 (GND), J16.51 (GND), J16.57 (GND), J16.63 (GND), J16.69 (GND), J16.75 (GND), J16.MP1, J16.MP2, R27.2, R28.2, R32.2
unnamed: D9.1 (K), J15.10 (DAS/~DSS/~LED1)
unnamed: D9.2 (A), R30.1
unnamed: J15.38 (DEVSLP), TP2.1
unnamed: J15.68 (SUSCLK), R29.1
unnamed: J15.69 (PEDET), R28.1
unnamed: J16.50 (SUSCLK), R33.1
unnamed: J16.54 (~W_DISABLE2), R35.2
unnamed: J16.56 (~W_DISABLE1), R34.1
PCIE_RX_0+: J16.41 (PERp0)
PCIE_RX_0-: J16.43 (PERn0)
PCIE_RX_1+: J15.43 (PERp0/SATA-B-)
PCIE_RX_1-: J15.41 (PERn0/SATA-B+)
PCIE_TX_0+: C55.1
PCIE_TX_0-: C56.1
PCIE_TX_1+: C49.1
PCIE_TX_1-: C50.1
REFCLKE+: J16.47 (REFCLKp0)
REFCLKE-: J16.49 (REFCLKn0)
REFCLKM+: J15.55 (REFCLKp)
REFCLKM-: J15.53 (REFCLKn)
SUSCLK: R29.2, R33.2
USB_2_P7+: J16.3 (USB_D+)
USB_2_P7-: J16.5 (USB_D-)
~CLKREQE: J16.53 (~CLKREQ0), R32.1
~CLKREQM: J15.52 (~CLKREQ), R27.1
~PLT_RST: J15.50 (~PERST), J16.52 (~PERST0)
~WAKE: J15.54 (~PEWAKE), J16.55 (~PEWAKE0)

Notes on the sheet:
To be grounded for SATA, No Connect for PCIe
SSD active LED
32.768kHz clock for low power mode
