LtBrain/MuBook/hardware/v.1/PCIe x4.kicad_sch

## KiCad design hardware/v.1/PCIe x4.kicad_sch (2025-07-31)

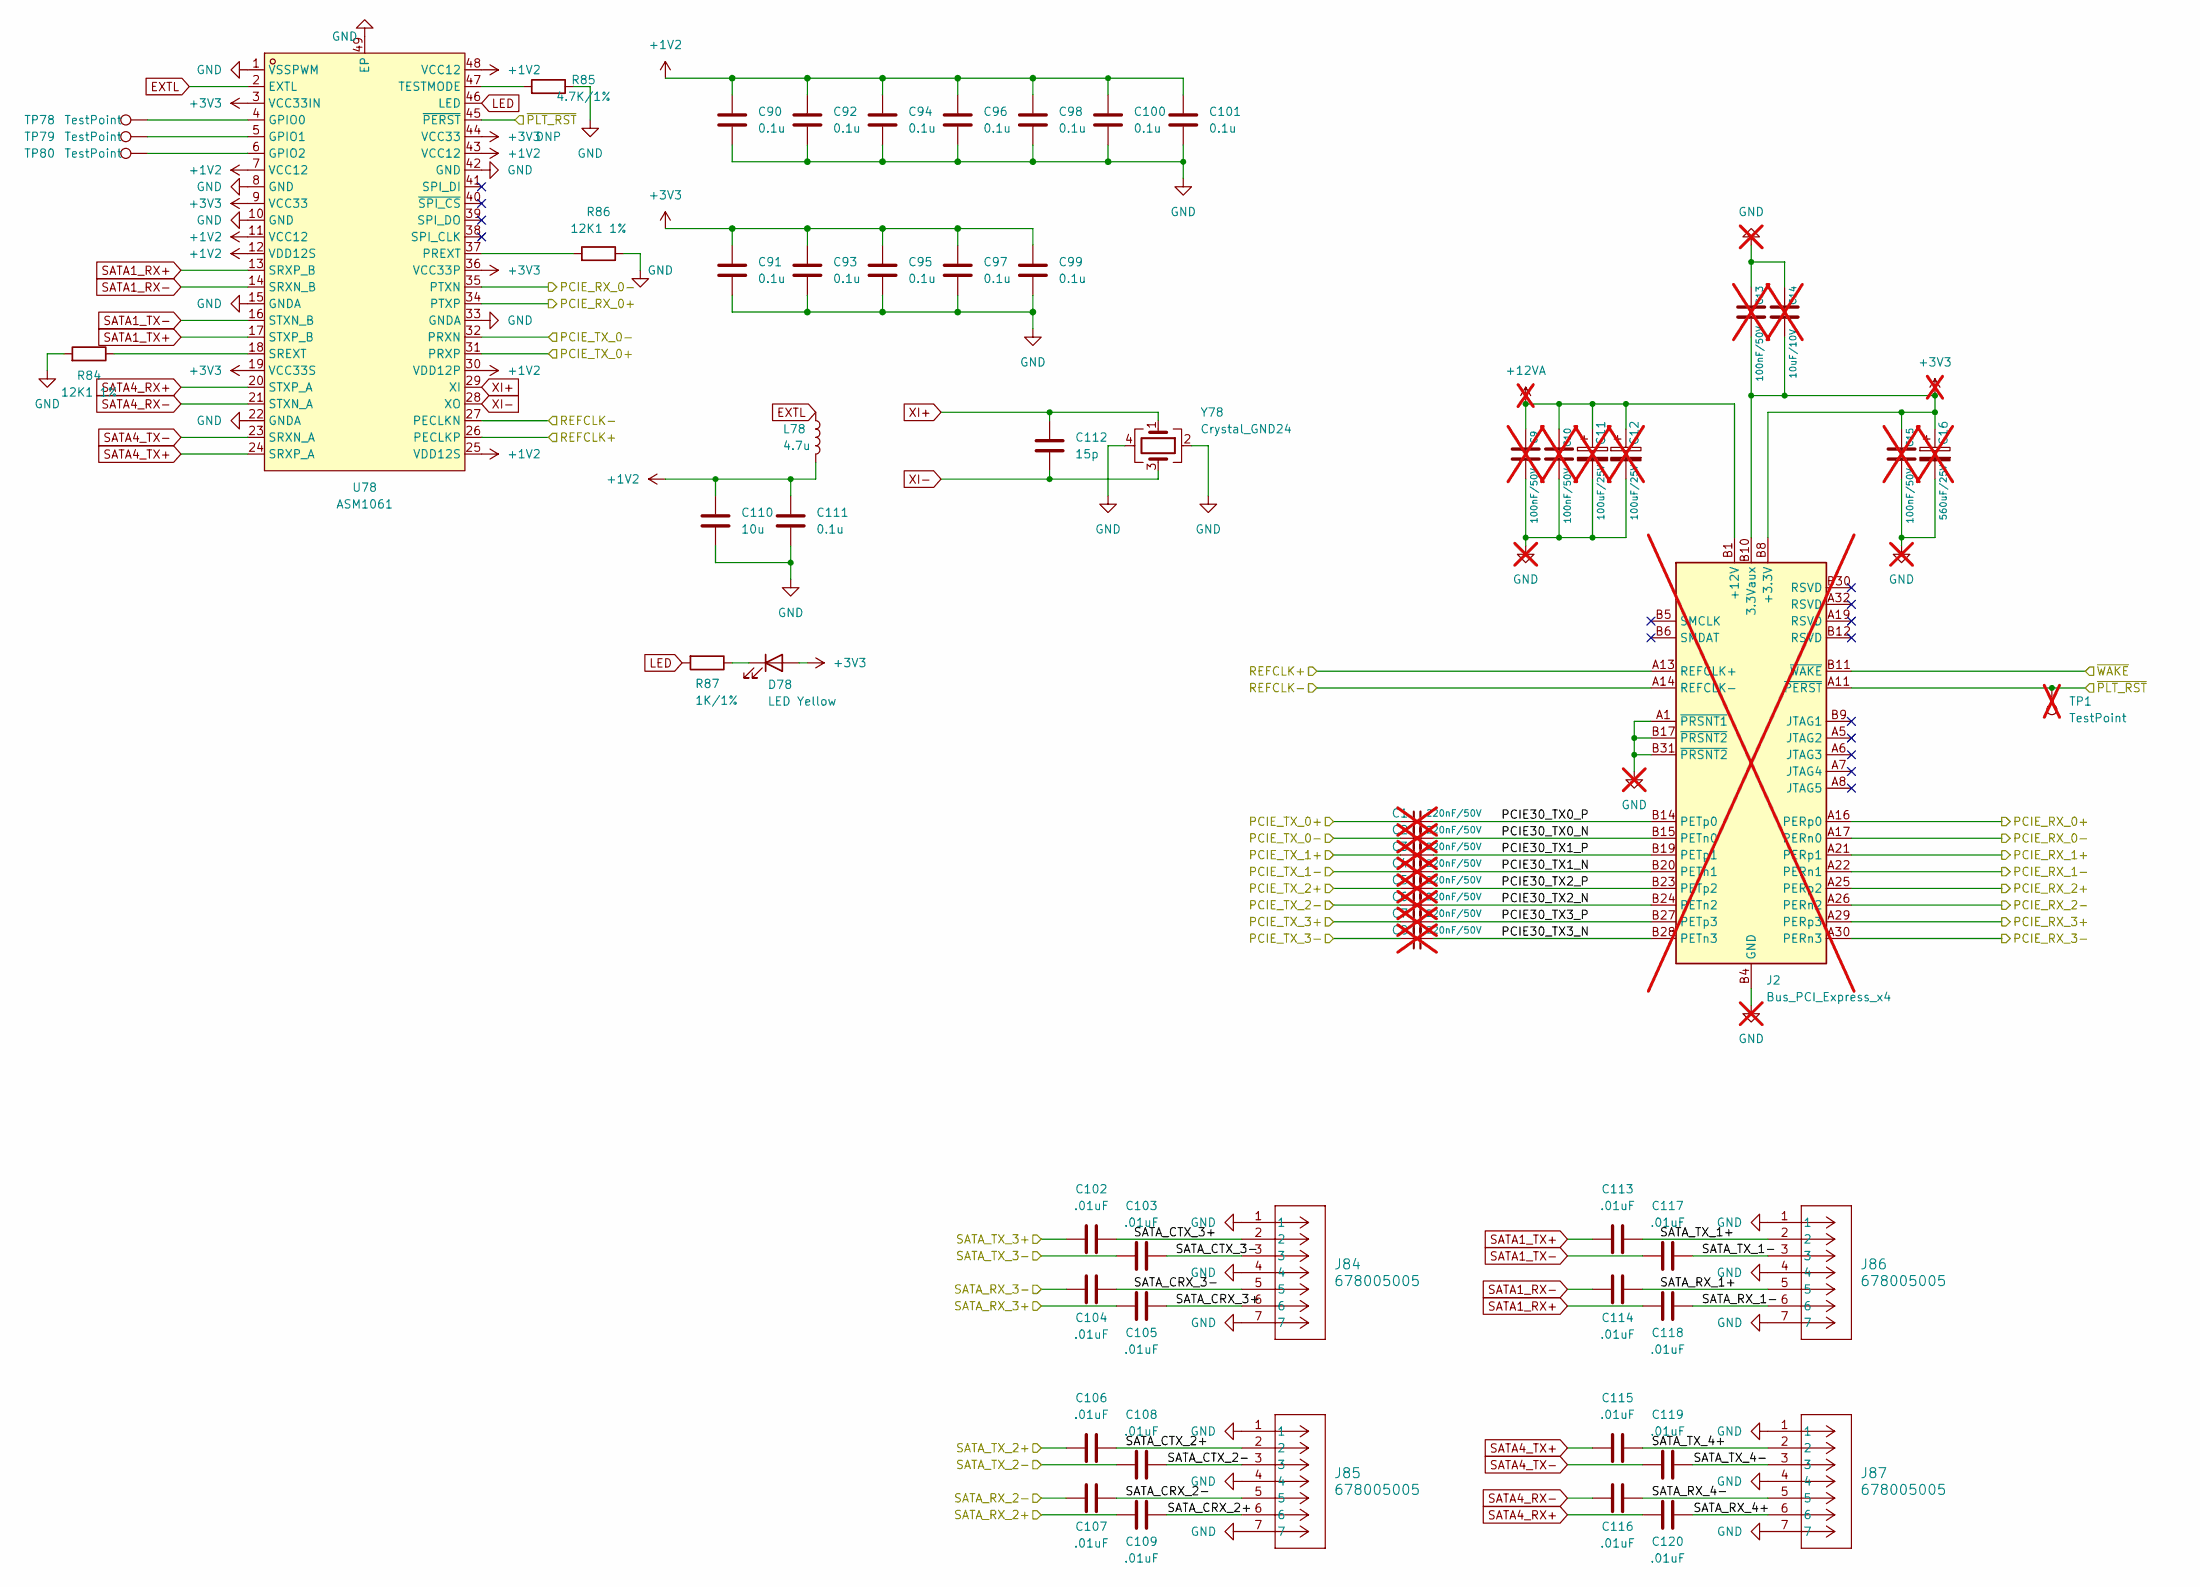
[picture p21: schematic PCIe x4.kicad_sch]

Parts:
C1, C2, C3, C4, C5, C6, C7, C8: 220nF/50V; C_0402_1005Metric; not fitted
C9, C10, C13, C15: 100nF/50V; C_0402_1005Metric; not fitted
C11, C12: 100uF/25V; CP_Elec_6.3x7.7; not fitted
C14: 10uF/10V; C_0402_1005Metric; not fitted
C16: 560uF/25V; CP_Elec_6.3x7.7; not fitted
C90, C91, C92, C93, C94, C95, C96, C97, C98, C99, C100, C101, C111: 0.1u; C_0402_1005Metric; MFG_PN GCM155R71C104KA55D; DigiKey_PN 490-4759-1-ND
C102, C103, C104, C105, C106, C107, C108, C109, C113, C114, C115, C116, C117, C118, C119, C120: .01uF; C_0402_1005Metric; MFG_PN GCM155R71C104KA55D; DigiKey_PN 490-4759-1-ND
C110: 10u; C_0805_2012Metric; MFG_PN GRM21BR70J106KA73L; DigiKey_PN 490-GRM21BR70J106KA73LCT-ND
C112: 15p; C_0402_1005Metric; MFG_PN GCM1555C1H150JA16D; DigiKey_PN 490-11147-1-ND
D78: LED Yellow; LED_0603_1608Metric; MFG_PN SML-D12Y1WT86; DigiKey_PN SML-D12Y1WT86CT-ND
J2: Bus_PCI_Express_x4; PCIe_x4_Gen3Slot_Connectors; not fitted
J84, J85, J86, J87: 678005005; CONN_67800-5005_MOL
L78: 4.7u; L_1008_2520Metric; MFG_PN CVH252009-4R7M; DigiKey_PN CVH252009-4R7MCT-ND
R84, R86: 12K1 1%; R_0402_1005Metric; MFG_PN RC0402FR-0712K1L; DigiKey_PN 311-12.1KLRCT-ND
R85: 4.7K/1%; R_0402_1005Metric; MFG_PN RC0402JR-074K7L; DigiKey_PN 311-4.7KJRCT-ND
R87: 1K/1%; R_0402_1005Metric; MFG_PN RC0402JR-071KL; DigiKey_PN 311-1.0KJRCT-ND
TP1: TestPoint; TestPoint_Pad_D1.5mm; not fitted
TP78, TP79, TP80: TestPoint; TestPoint_Pad_D1.5mm
U78: ASM1061; QFN-48_L7.0-W7.0-P0.50-BL-EP4.1; LCSC Part C2835235
Y78: Crystal_GND24; Crystal_SMD_3225-4Pin_3.2x2.5mm; MFG_PN CX3225SB20000H0FLJCC; DigiKey_PN 1253-1744-1-ND

Connections:
+1V2: C90.1, C92.1, C94.1, C96.1, C98.1, C100.1, C101.1, C110.1, C111.1, L78.2, U78.7 (VCC12), U78.11 (VCC12), U78.12 (VDD12S), U78.25 (VDD12S), U78.30 (VDD12P), U78.43 (VCC12), U78.48 (VCC12)
+3V3: C13.2, C14.2, C15.1, C16.1, C91.1, C93.1, C95.1, C97.1, C99.1, D78.2 (A), J2.A9 (+3.3V), J2.A10 (+3.3V), J2.B8 (+3.3V), J2.B10 (3.3Vaux), U78.3 (VCC33IN), U78.9 (VCC33), U78.19 (VCC33S), U78.36 (VCC33P), U78.44 (VCC33)
+12VA: C9.1, C10.1, C11.1, C12.1, J2.A2 (+12V), J2.A3 (+12V), J2.B1 (+12V), J2.B2 (+12V), J2.B3 (+12V)
EXTL: L78.1, U78.2 (EXTL)
GND: C9.2, C10.2, C11.2, C12.2, C13.1, C14.1, C15.2, C16.2, C90.2, C91.2, C92.2, C93.2, C94.2, C95.2, C96.2, C97.2, C98.2, C99.2, C100.2, C101.2, C110.2, C111.2, J2.A1 (~PRSNT1), J2.A4 (GND), J2.A12 (GND), J2.A15 (GND), J2.A18 (GND), J2.A20 (GND), J2.A23 (GND), J2.A24 (GND), J2.A27 (GND), J2.A28 (GND), J2.A31 (GND), J2.B4 (GND), J2.B7 (GND), J2.B13 (GND), J2.B16 (GND), J2.B17 (~PRSNT2), J2.B18 (GND), J2.B21 (GND), J2.B22 (GND), J2.B25 (GND), J2.B26 (GND), J2.B29 (GND), J2.B31 (~PRSNT2), J2.B32 (GND), J84.1, J84.4, J84.7, J85.1, J85.4, J85.7, J86.1, J86.4, J86.7, J87.1, J87.4, J87.7, R84.2, R85.1, R86.1, U78.1 (VSSPWM), U78.8 (GND), U78.10 (GND), U78.15 (GNDA), U78.22 (GNDA), U78.33 (GNDA), U78.42 (GND), U78.49 (EP), Y78.2, Y78.4
LED: R87.2, U78.46 (LED)
unnamed: D78.1 (K), R87.1
unnamed: R84.1, U78.18 (SREXT)
unnamed: R85.2, U78.47 (TESTMODE)
unnamed: R86.2, U78.37 (PREXT)
unnamed: TP78.1, U78.4 (GPIO0)
unnamed: TP79.1, U78.5 (GPIO1)
unnamed: TP80.1, U78.6 (GPIO2)
PCIE30_TX0_N: C2.2, J2.B15 (PETn0)
PCIE30_TX0_P: C1.2, J2.B14 (PETp0)
PCIE30_TX1_N: C4.2, J2.B20 (PETn1)
PCIE30_TX1_P: C3.2, J2.B19 (PETp1)
PCIE30_TX2_N: C6.2, J2.B24 (PETn2)
PCIE30_TX2_P: C5.2, J2.B23 (PETp2)
PCIE30_TX3_N: C8.2, J2.B28 (PETn3)
PCIE30_TX3_P: C7.2, J2.B27 (PETp3)
PCIE_RX_0+: J2.A16 (PERp0), U78.34 (PTXP)
PCIE_RX_0-: J2.A17 (PERn0), U78.35 (PTXN)
PCIE_RX_1+: J2.A21 (PERp1)
PCIE_RX_1-: J2.A22 (PERn1)
PCIE_RX_2+: J2.A25 (PERp2)
PCIE_RX_2-: J2.A26 (PERn2)
PCIE_RX_3+: J2.A29 (PERp3)
PCIE_RX_3-: J2.A30 (PERn3)
PCIE_TX_0+: C1.1, U78.31 (PRXP)
PCIE_TX_0-: C2.1, U78.32 (PRXN)
PCIE_TX_1+: C3.1
PCIE_TX_1-: C4.1
PCIE_TX_2+: C5.1
PCIE_TX_2-: C6.1
PCIE_TX_3+: C7.1
PCIE_TX_3-: C8.1
REFCLK+: J2.A13 (REFCLK+), U78.26 (PECLKP)
REFCLK-: J2.A14 (REFCLK-), U78.27 (PECLKN)
SATA1_RX+: C118.1, U78.13 (SRXP_B)
SATA1_RX-: C114.1, U78.14 (SRXN_B)
SATA1_TX+: C113.1, U78.17 (STXP_B)
SATA1_TX-: C117.1, U78.16 (STXN_B)
SATA4_RX+: C120.1, U78.20 (STXP_A)
SATA4_RX-: C116.1, U78.21 (STXN_A)
SATA4_TX+: C115.1, U78.24 (SRXP_A)
SATA4_TX-: C119.1, U78.23 (SRXN_A)
SATA_CRX_2+: C109.1, J85.6
SATA_CRX_2-: C107.1, J85.5
SATA_CRX_3+: C105.2, J84.6
SATA_CRX_3-: C104.2, J84.5
SATA_CTX_2+: C106.1, J85.2
SATA_CTX_2-: C108.1, J85.3
SATA_CTX_3+: C102.2, J84.2
SATA_CTX_3-: C103.2, J84.3
SATA_RX_1+: C114.2, J86.5
SATA_RX_1-: C118.2, J86.6
SATA_RX_2+: C109.2
SATA_RX_2-: C107.2
SATA_RX_3+: C105.1
SATA_RX_3-: C104.1
SATA_RX_4+: C120.2, J87.6
SATA_RX_4-: C116.2, J87.5
SATA_TX_1+: C113.2, J86.2
SATA_TX_1-: C117.2, J86.3
SATA_TX_2+: C106.2
SATA_TX_2-: C108.2
SATA_TX_3+: C102.1
SATA_TX_3-: C103.1
SATA_TX_4+: C115.2, J87.2
SATA_TX_4-: C119.2, J87.3
XI+: C112.1, U78.29 (XI), Y78.1
XI-: C112.2, U78.28 (XO), Y78.3
~PLT_RST: J2.A11 (~PERST), TP1.1, U78.45 (~PERST)
~WAKE: J2.B11 (~WAKE)
