LtBrain/MuBook/hardware/v.1/PSU.kicad_sch

## KiCad design hardware/v.1/PSU.kicad_sch (2025-08-01)

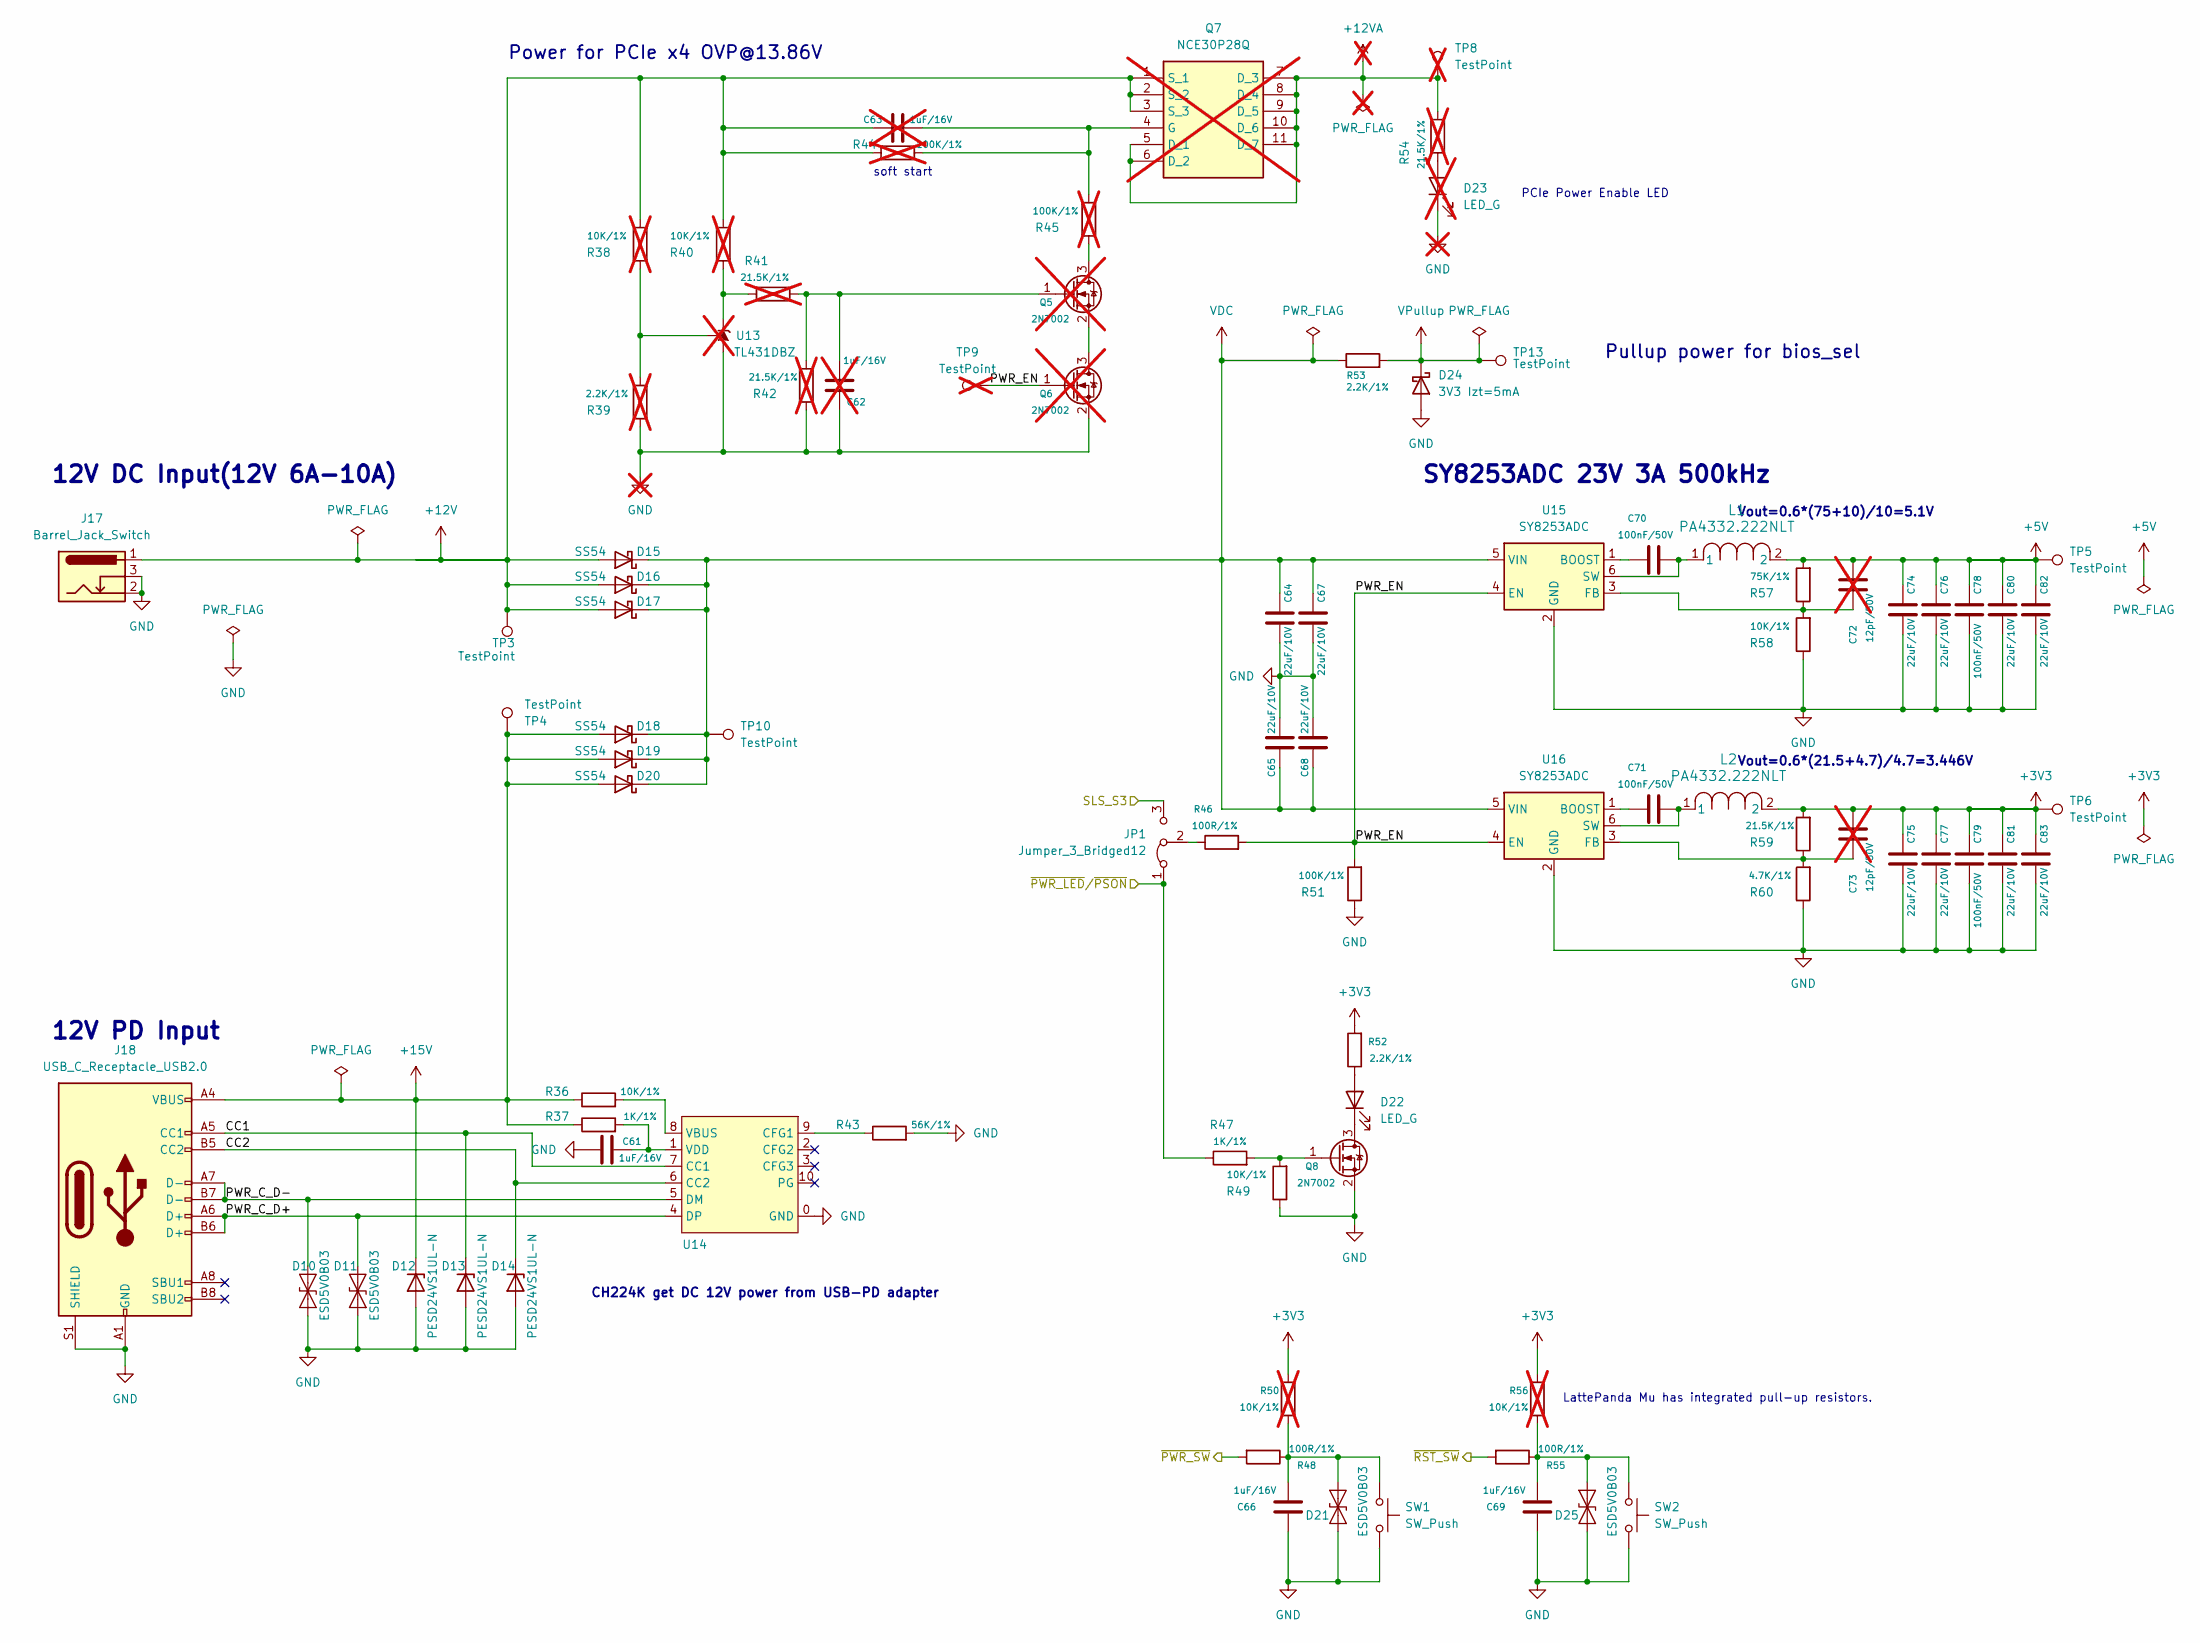
[picture p22: schematic PSU.kicad_sch]

Parts:
C61, C66, C69: 1uF/16V; C_0402_1005Metric
C62, C63: 1uF/16V; C_0402_1005Metric; not fitted
C64, C65, C67, C68, C74, C75, C76, C77, C80, C81, C82, C83: 22uF/10V; C_0603_1608Metric
C70, C71, C78, C79: 100nF/50V; C_0402_1005Metric
C72, C73: 12pF/50V; C_0402_1005Metric; not fitted
D10, D11, D21, D25: ESD5V0B03; D_0402_1005Metric
D12, D13, D14: PESD24VS1UL-N; D_0402_1005Metric
D15, D16, D17, D18, D19, D20: SS54; D_SMA
D22: LED_G; LED_0603_1608Metric
D23: LED_G; LED_0603_1608Metric; not fitted
D24: 3V3 Izt=5mA; D_SOD-323
J17: Barrel_Jack_Switch; DC_Jack_DC007B_30V_10A
J18: USB_C_Receptacle_USB2.0; USB_C_Receptacle_JAE_DX07S016JA1R1500
JP1: Jumper_3_Bridged12; PinHeader_1x03_P2.54mm_Vertical
L1, L2: PA4332.222NLT; IND_PA4332.222NLT_PUL
Q5, Q6: 2N7002; SOT-23; not fitted
Q7: NCE30P28Q; MOSFET_PDFN8_3.3x3.3; not fitted
Q8: 2N7002; SOT-23
R36, R49, R58: 10K/1%; R_0402_1005Metric
R37, R47: 1K/1%; R_0402_1005Metric
R38, R40, R50, R56: 10K/1%; R_0402_1005Metric; not fitted
R39: 2.2K/1%; R_0402_1005Metric; not fitted
R41, R42, R54: 21.5K/1%; R_0402_1005Metric; not fitted
R43: 56K/1%; R_0402_1005Metric
R44, R45: 100K/1%; R_0402_1005Metric; not fitted
R46, R48, R55: 100R/1%; R_0402_1005Metric
R51: 100K/1%; R_0402_1005Metric
R52, R53: 2.2K/1%; R_0402_1005Metric
R57: 75K/1%; R_0402_1005Metric
R59: 21.5K/1%; R_0402_1005Metric
R60: 4.7K/1%; R_0402_1005Metric
SW1, SW2: SW_Push; SW_Push_6x6x6
TP3, TP4, TP5, TP6, TP10, TP13: TestPoint; TestPoint_Pad_D1.5mm
TP8, TP9: TestPoint; TestPoint_Pad_D1.5mm; not fitted
U13: TL431DBZ; SOT-23; not fitted
U14: CH224K; ESSOP-10-1EP_3.9x5mm_P1.0mm_EP3.2x2.3
U15, U16: SY8253ADC; TSOT-23-6

Connections:
+3V3: C73.1, C75.2, C77.2, C79.1, C81.2, C83.2, L2.2, R50.2, R52.2, R56.2, R59.2, TP6.1
+5V: C72.1, C74.2, C76.2, C78.1, C80.2, C82.2, L1.2, R57.2, TP5.1
+12V: C63.2, D15.2 (A), D16.2 (A), D17.2 (A), J17.1, Q7.1 (S_1), Q7.2 (S_2), Q7.3 (S_3), R38.2, R40.2, R44.2, TP3.1
+12VA: Q7.5 (D_1), Q7.6 (D_2), Q7.7 (D_3), Q7.8 (D_4), Q7.9 (D_5), Q7.10 (D_6), Q7.11 (D_7), R54.1, TP8.1
+15V: D12.1 (K), D18.2 (A), D19.2 (A), D20.2 (A), J18.A4 (VBUS), J18.A9 (VBUS), J18.B4 (VBUS), J18.B9 (VBUS), R36.1, R37.1, TP4.1
CC1: D13.1 (K), J18.A5 (CC1), U14.7 (CC1)
CC2: D14.1 (K), J18.B5 (CC2), U14.6 (CC2)
GND: C61.2, C62.2, C64.1, C65.1, C66.2, C67.1, C68.1, C69.2, C74.1, C75.1, C76.1, C77.1, C78.2, C79.2, C80.1, C81.1, C82.1, C83.1, D10.1 (A1), D11.1 (A1), D12.2 (A), D13.2 (A), D14.2 (A), D21.1 (A1), D23.1 (K), D24.2 (A), D25.1 (A1), J17.2, J17.3, J18.A1 (GND), J18.A12 (GND), J18.B1 (GND), J18.B12 (GND), J18.S1 (SHIELD), Q6.2 (S), Q8.2 (S), R39.1, R42.1, R43.2, R49.1, R51.1, R58.1, R60.1, SW1.2, SW2.2, U13.3 (A), U14.0 (GND), U15.2 (GND), U16.2 (GND)
unnamed: C61.1, R37.2, U14.1 (VDD)
unnamed: C62.1, Q5.1 (G), R41.1, R42.2
unnamed: C63.1, Q7.4 (G), R44.1, R45.2
unnamed: C66.1, D21.2 (A2), R48.1, R50.1, SW1.1
unnamed: C69.1, D25.2 (A2), R55.1, R56.1, SW2.1
unnamed: C70.1, L1.1, U15.6 (SW)
unnamed: C70.2, U15.1 (BOOST)
unnamed: C71.1, L2.1, U16.6 (SW)
unnamed: C71.2, U16.1 (BOOST)
unnamed: C72.2, R57.1, R58.2, U15.3 (FB)
unnamed: C73.2, R59.1, R60.2, U16.3 (FB)
unnamed: D22.1 (K), Q8.3 (D)
unnamed: D22.2 (A), R52.1
unnamed: D23.2 (A), R54.2
unnamed: JP1.2 (C), R46.1
unnamed: Q5.2 (S), Q6.3 (D)
unnamed: Q5.3 (D), R45.1
unnamed: Q8.1 (G), R47.2, R49.2
unnamed: R36.2, U14.8 (VBUS)
unnamed: R38.1, R39.2, U13.2 (REF)
unnamed: R40.1, R41.2, U13.1 (K)
unnamed: R43.1, U14.9 (CFG1)
PWR_C_D+: D11.2 (A2), J18.A6 (D+), J18.B6 (D+), U14.4 (DP)
PWR_C_D-: D10.2 (A2), J18.A7 (D-), J18.B7 (D-), U14.5 (DM)
PWR_EN: Q6.1 (G), R46.2, R51.2, TP9.1, U15.4 (EN), U16.4 (EN)
SLS_S3: JP1.3 (B)
VDC: C64.2, C65.2, C67.2, C68.2, D15.1 (K), D16.1 (K), D17.1 (K), D18.1 (K), D19.1 (K), D20.1 (K), R53.1, TP10.1, U15.5 (VIN), U16.5 (VIN)
VPullup: D24.1 (K), R53.2, TP13.1
~PWR_LED/~PSON: JP1.1 (A), R47.1
~PWR_SW: R48.2
~RST_SW: R55.2

Notes on the sheet:
soft start
12V PD Input
SY8253ADC 23V 3A 500kHz
LattePanda Mu has integrated pull-up resistors.
Power for PCIe x4 OVP@13.86V
Vout=0.6*(75+10)/10=5.1V
12V DC Input(12V 6A-10A)
CH224K get DC 12V power from USB-PD adapter
PCIe Power Enable LED
Pullup power for bios_sel
Vout=0.6*(21.5+4.7)/4.7=3.446V
