LtBrain/MuBook/hardware/v.1/USB2.0&USB3.0.kicad_sch

## KiCad design hardware/v.1/USB2.0&USB3.0.kicad_sch (2025-08-01)

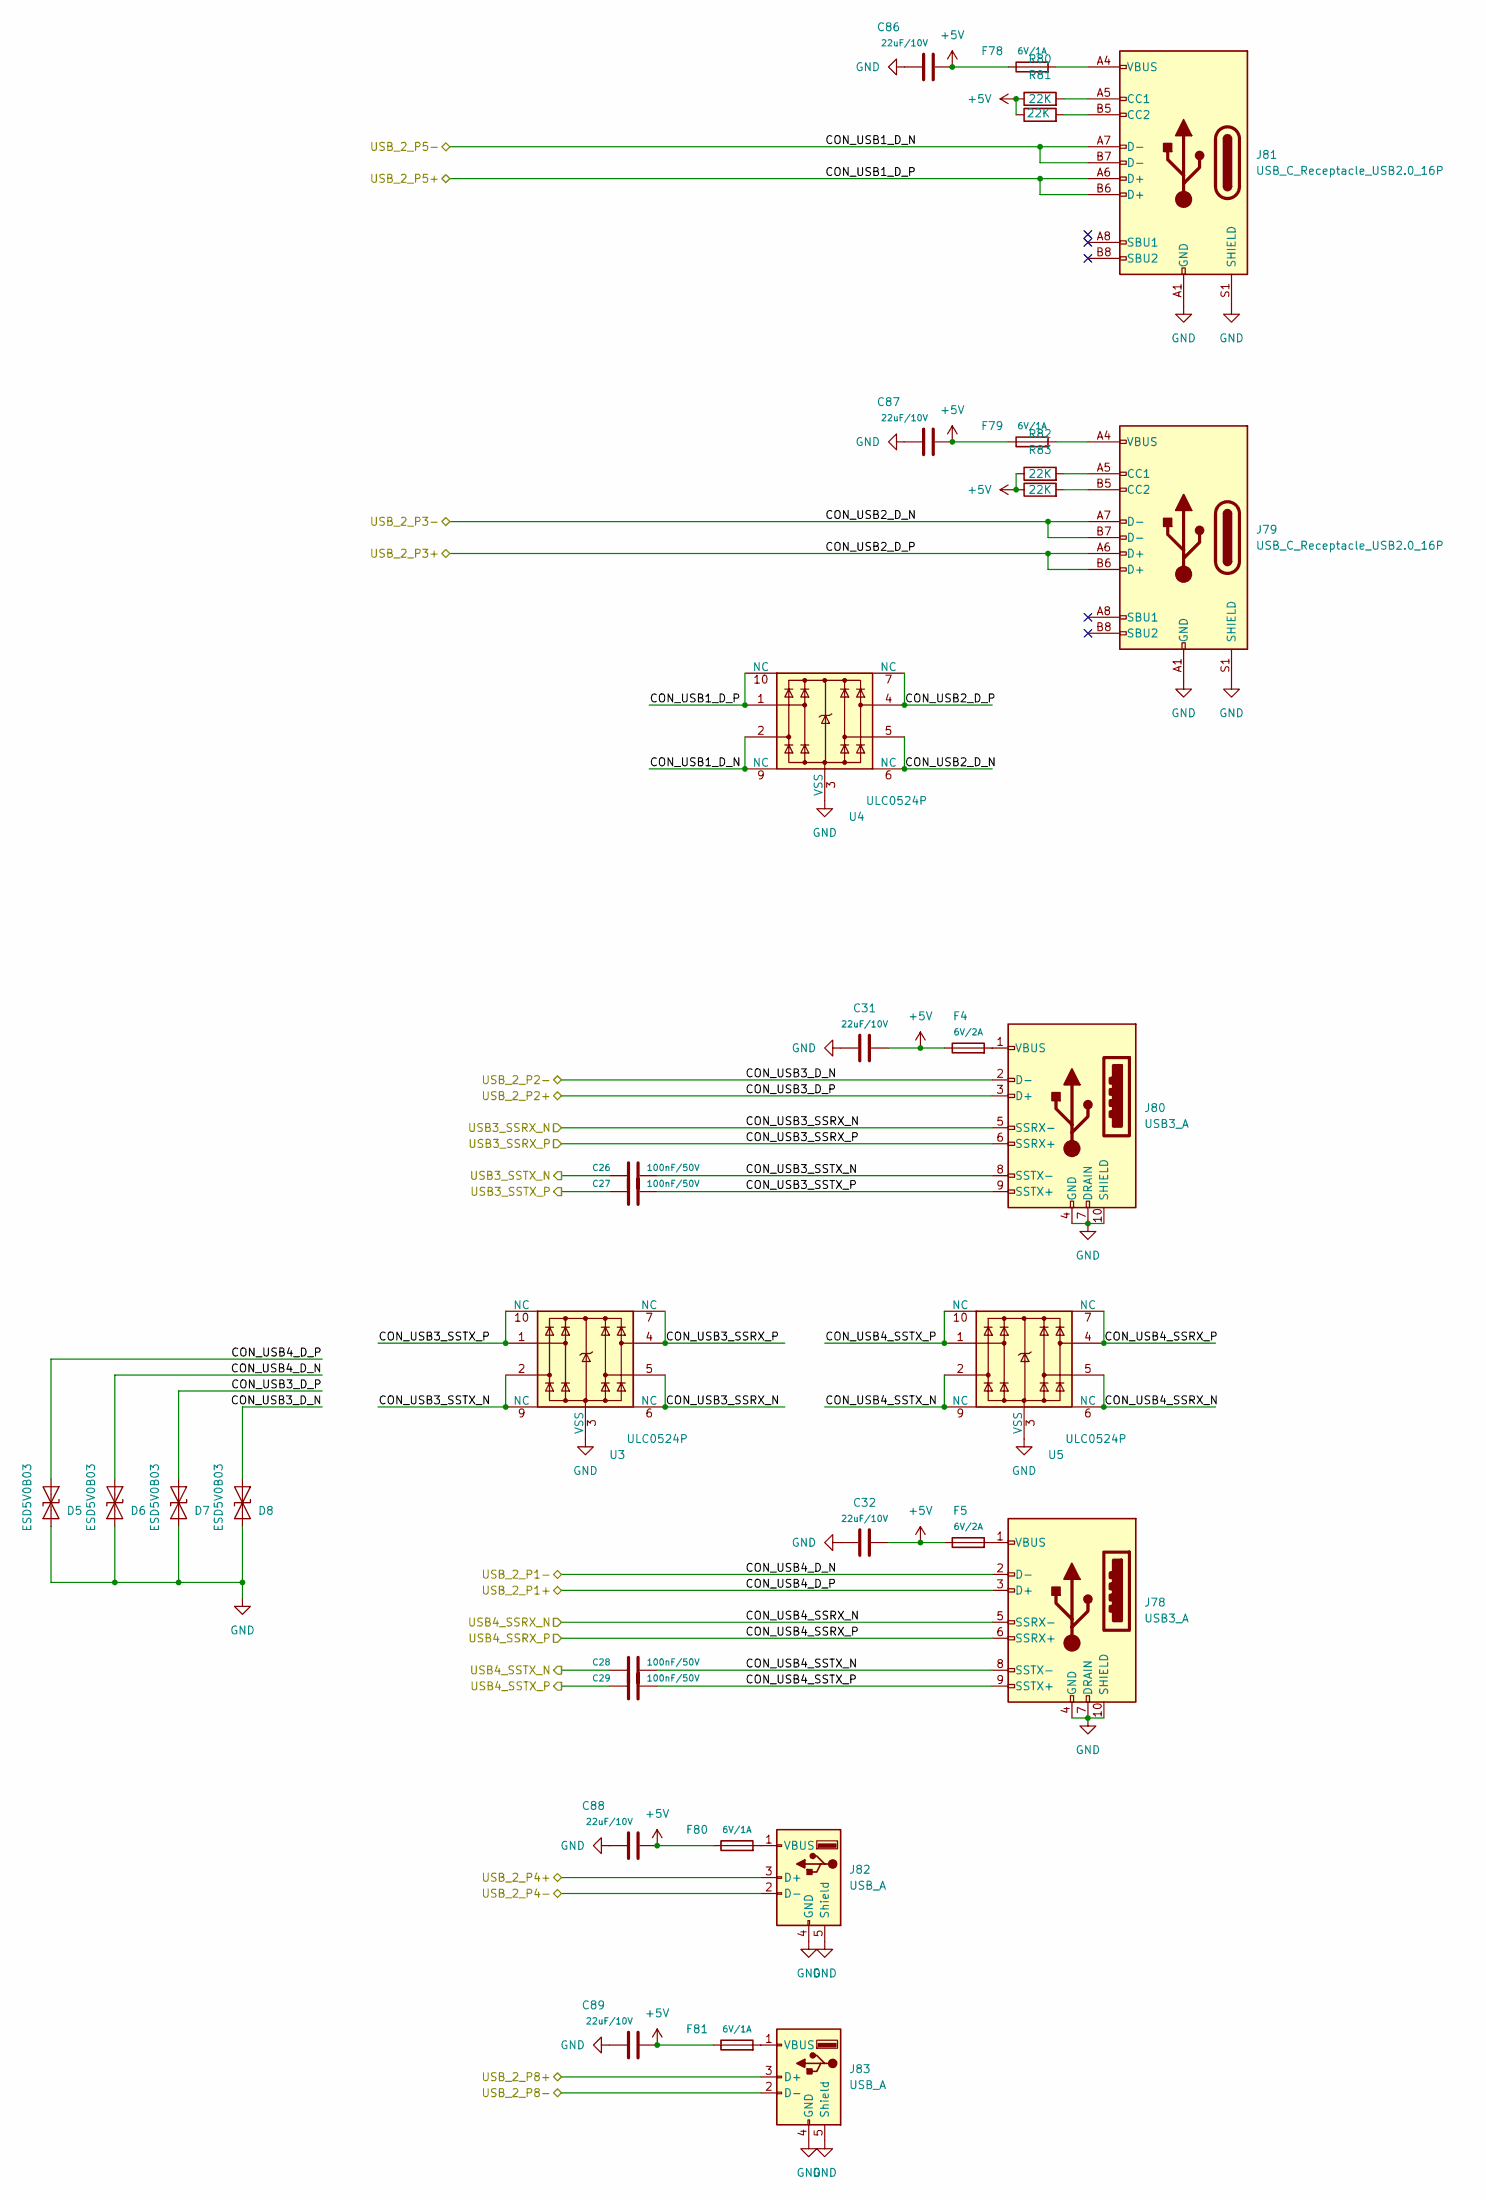
[picture p23: schematic USB2.0&USB3.0.kicad_sch]

Parts:
C26, C27, C28, C29: 100nF/50V; C_0402_1005Metric
C31, C32, C86, C87, C88, C89: 22uF/10V; C_0603_1608Metric
D5, D6, D7, D8: ESD5V0B03; D_0402_1005Metric
F4: 6V/2A; R_0805_2012Metric
F5: 6V/2A; Fuse_0805_2012Metric
F78, F79, F80, F81: 6V/1A; Fuse_0805_2012Metric
J78, J80: USB3_A; USB3_A_Receptacle_Wuerth_692122030100
J79, J81: USB_C_Receptacle_USB2.0_16P; USB_C_Receptacle_JAE_DX07S016JA1R1500
J82, J83: USB_A; USB_A_Receptacle_GCT_USB1046
R80, R81, R82, R83: 22K; R_0402_1005Metric
U3, U4, U5: ULC0524P; Diodes_UDFN-10_1.0x2.5mm_P0.5mm

Connections:
+5V: C31.2, C32.2, C86.2, C87.2, C88.2, C89.2, F4.1, F5.1, F78.1, F79.1, F80.1, F81.1, R80.1, R81.1, R82.1, R83.1
CON_USB1_D_N: J81.A7 (D-), J81.B7 (D-), U4.2, U4.9 (NC)
CON_USB1_D_P: J81.A6 (D+), J81.B6 (D+), U4.1, U4.10 (NC)
CON_USB2_D_N: J79.A7 (D-), J79.B7 (D-), U4.5, U4.6 (NC)
CON_USB2_D_P: J79.A6 (D+), J79.B6 (D+), U4.4, U4.7 (NC)
CON_USB3_D_N: D8.2 (A2), J80.2 (D-)
CON_USB3_D_P: D7.2 (A2), J80.3 (D+)
CON_USB3_SSRX_N: J80.5 (SSRX-), U3.5, U3.6 (NC)
CON_USB3_SSRX_P: J80.6 (SSRX+), U3.4, U3.7 (NC)
CON_USB3_SSTX_N: C26.2, J80.8 (SSTX-), U3.2, U3.9 (NC)
CON_USB3_SSTX_P: C27.2, J80.9 (SSTX+), U3.1, U3.10 (NC)
CON_USB4_D_N: D6.2 (A2), J78.2 (D-)
CON_USB4_D_P: D5.2 (A2), J78.3 (D+)
CON_USB4_SSRX_N: J78.5 (SSRX-), U5.5, U5.6 (NC)
CON_USB4_SSRX_P: J78.6 (SSRX+), U5.4, U5.7 (NC)
CON_USB4_SSTX_N: C28.2, J78.8 (SSTX-), U5.2, U5.9 (NC)
CON_USB4_SSTX_P: C29.2, J78.9 (SSTX+), U5.1, U5.10 (NC)
GND: C31.1, C32.1, C86.1, C87.1, C88.1, C89.1, D5.1 (A1), D6.1 (A1), D7.1 (A1), D8.1 (A1), J78.4 (GND), J78.7 (DRAIN), J78.10 (SHIELD), J79.A1 (GND), J79.A12 (GND), J79.B1 (GND), J79.B12 (GND), J79.S1 (SHIELD), J80.4 (GND), J80.7 (DRAIN), J80.10 (SHIELD), J81.A1 (GND), J81.A12 (GND), J81.B1 (GND), J81.B12 (GND), J81.S1 (SHIELD), J82.4 (GND), J82.5 (Shield), J83.4 (GND), J83.5 (Shield), U3.3 (VSS), U3.8 (VSS), U4.3 (VSS), U4.8 (VSS), U5.3 (VSS), U5.8 (VSS)
unnamed: F4.2, J80.1 (VBUS)
unnamed: F5.2, J78.1 (VBUS)
unnamed: F78.2, J81.A4 (VBUS), J81.A9 (VBUS), J81.B4 (VBUS), J81.B9 (VBUS)
unnamed: F79.2, J79.A4 (VBUS), J79.A9 (VBUS), J79.B4 (VBUS), J79.B9 (VBUS)
unnamed: F80.2, J82.1 (VBUS)
unnamed: F81.2, J83.1 (VBUS)
unnamed: J79.A5 (CC1), R82.2
unnamed: J79.B5 (CC2), R83.2
unnamed: J81.A5 (CC1), R80.2
unnamed: J81.B5 (CC2), R81.2
USB3_SSTX_N: C26.1
USB3_SSTX_P: C27.1
USB4_SSTX_N: C28.1
USB4_SSTX_P: C29.1
USB_2_P4+: J82.3 (D+)
USB_2_P4-: J82.2 (D-)
USB_2_P8+: J83.3 (D+)
USB_2_P8-: J83.2 (D-)
