LtBrain/MuBook/hardware/v.1/[DFR1142]Lite Carrier for LattePanda Mu.kicad_sch

## KiCad design hardware/v.1/[DFR1142]Lite Carrier for LattePanda Mu.kicad_sch (2025-08-01)

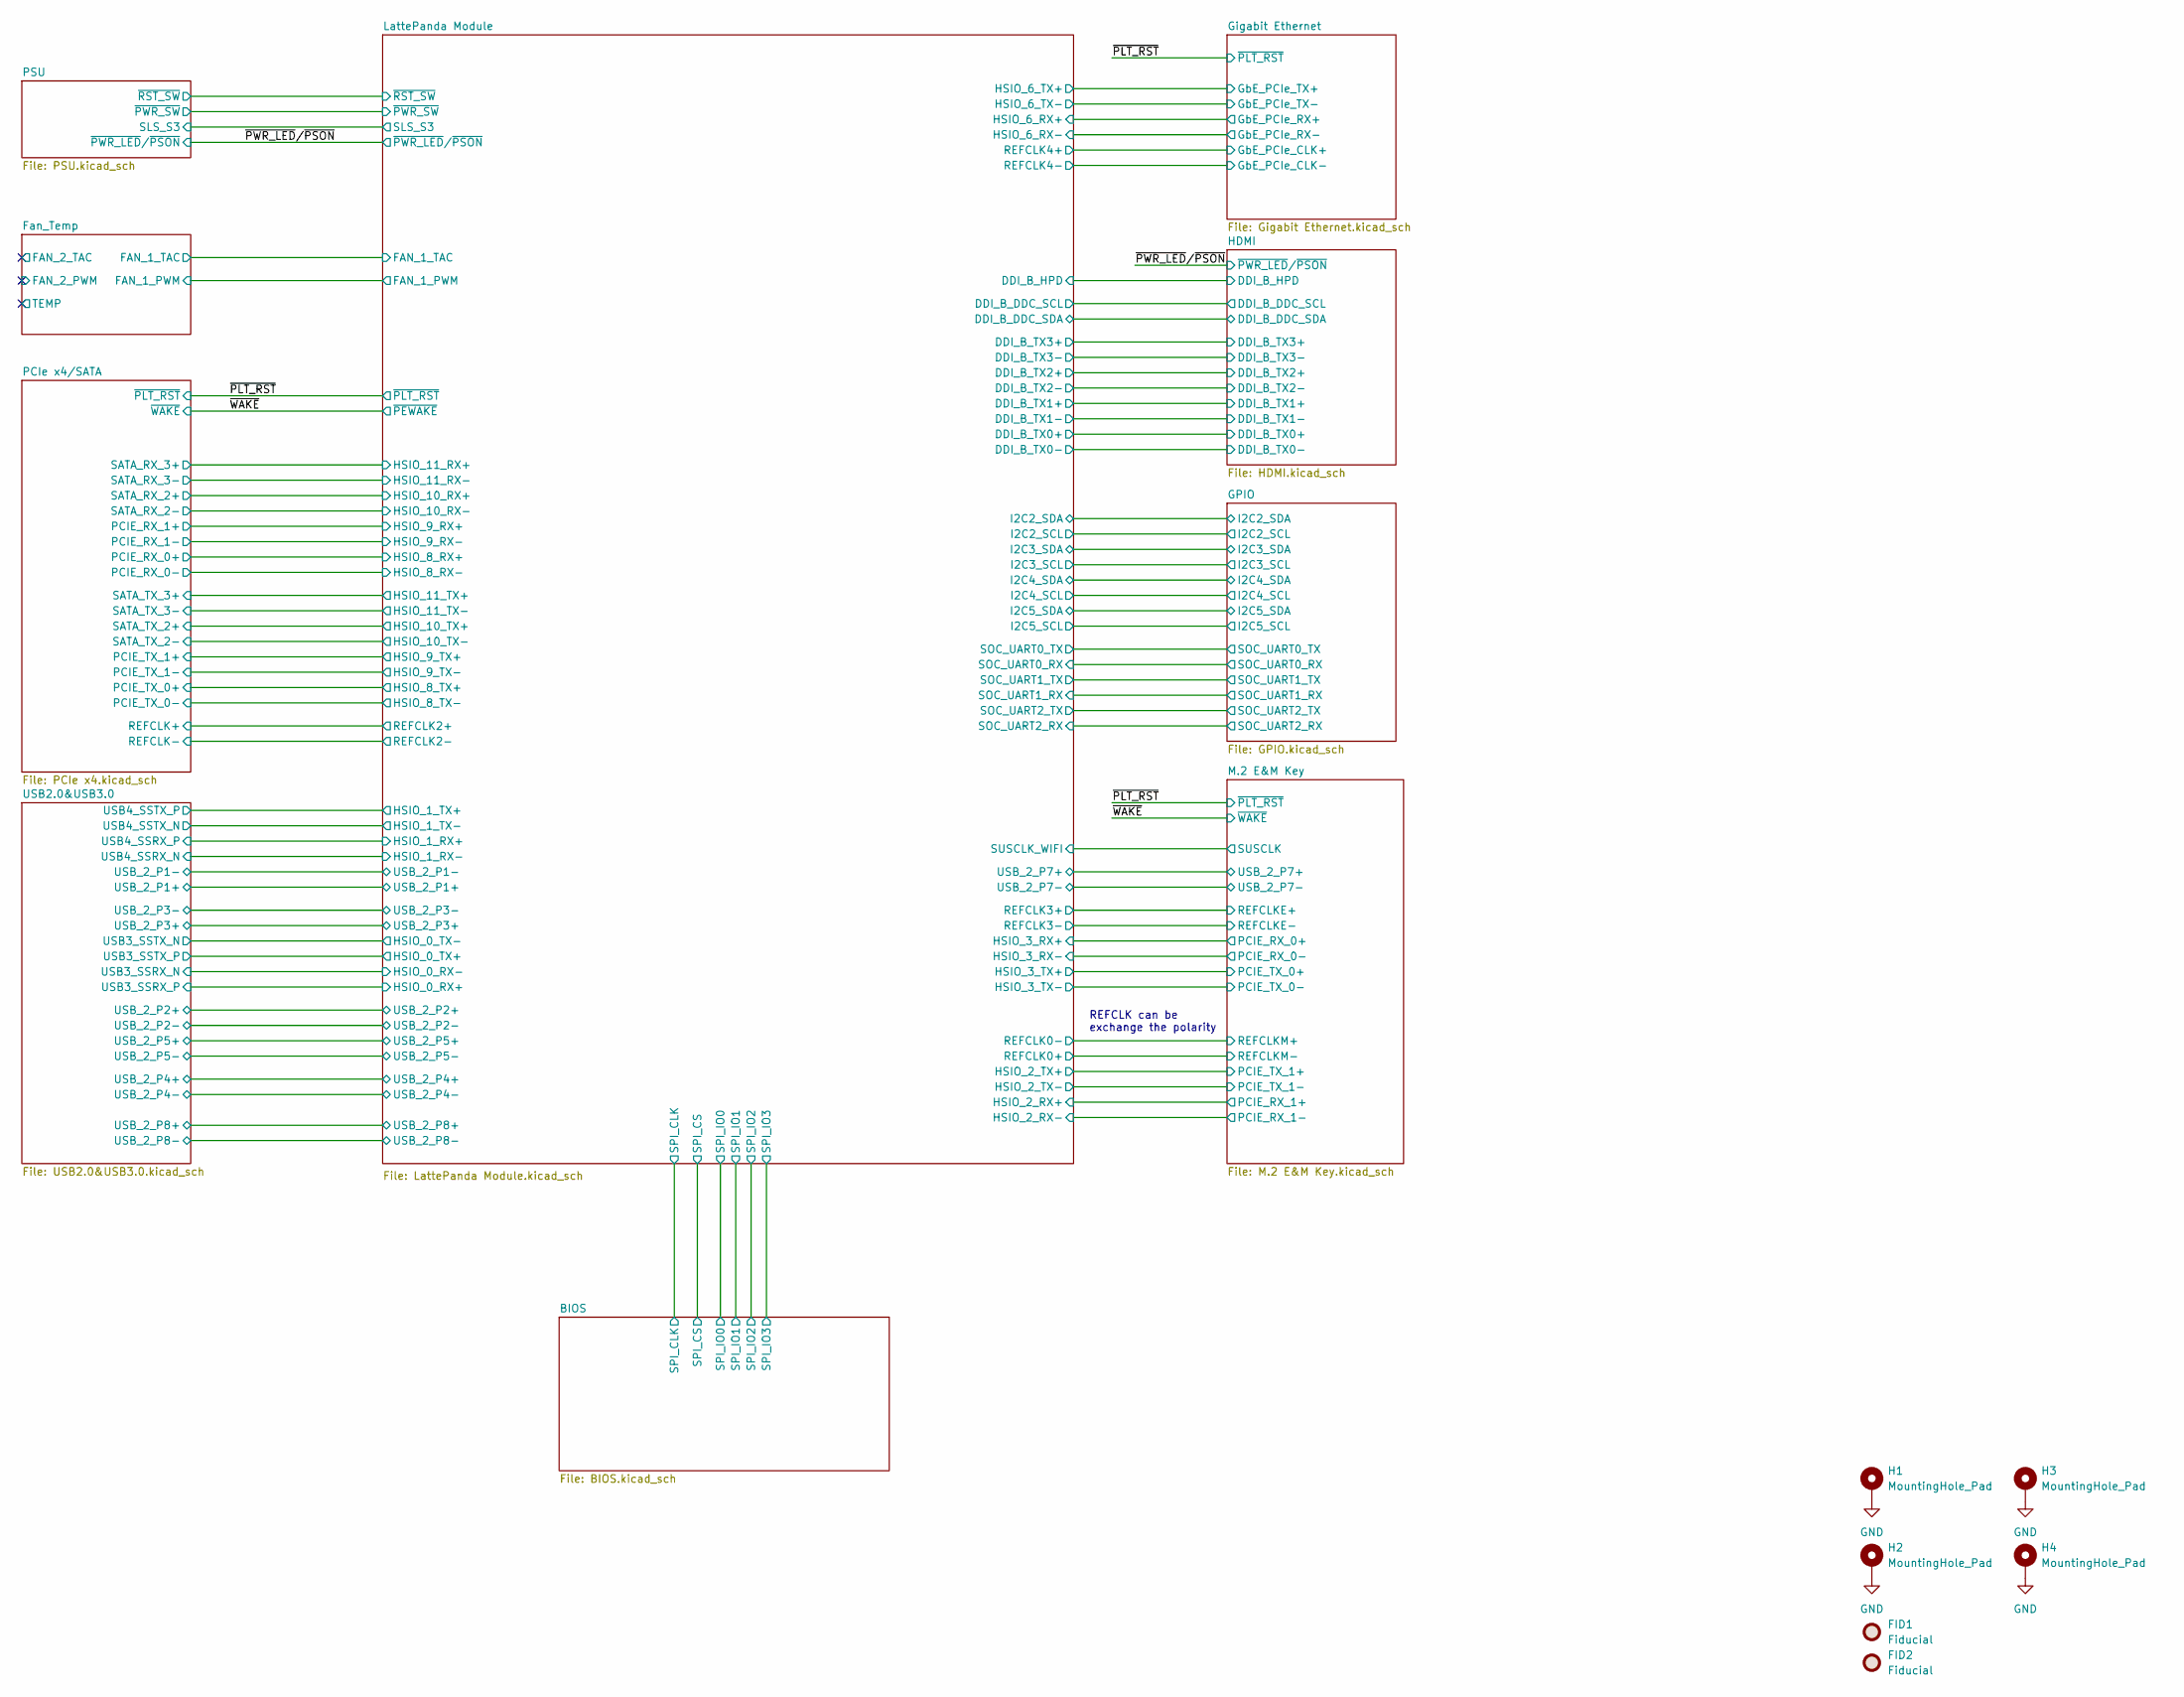
[picture p24: schematic [DFR1142]Lite Carrier for LattePanda Mu.kicad_sch]

Parts:
FID1, FID2: Fiducial; Fiducial_0.5mm_Mask1mm
H1: MountingHole_Pad; MountingHole_3.2mm_M3_Pad_Via
H2, H3, H4: MountingHole_Pad; MountingHole_2.2mm_M2_DIN965_Pad

Connections:
GND: H1.1, H2.1, H3.1, H4.1

Notes on the sheet:
REFCLK can be exchange the polarity
