LtBrain/MuBook/hardware/v.1/fan&temp.kicad_sch

## KiCad design hardware/v.1/fan&temp.kicad_sch (2025-07-12)

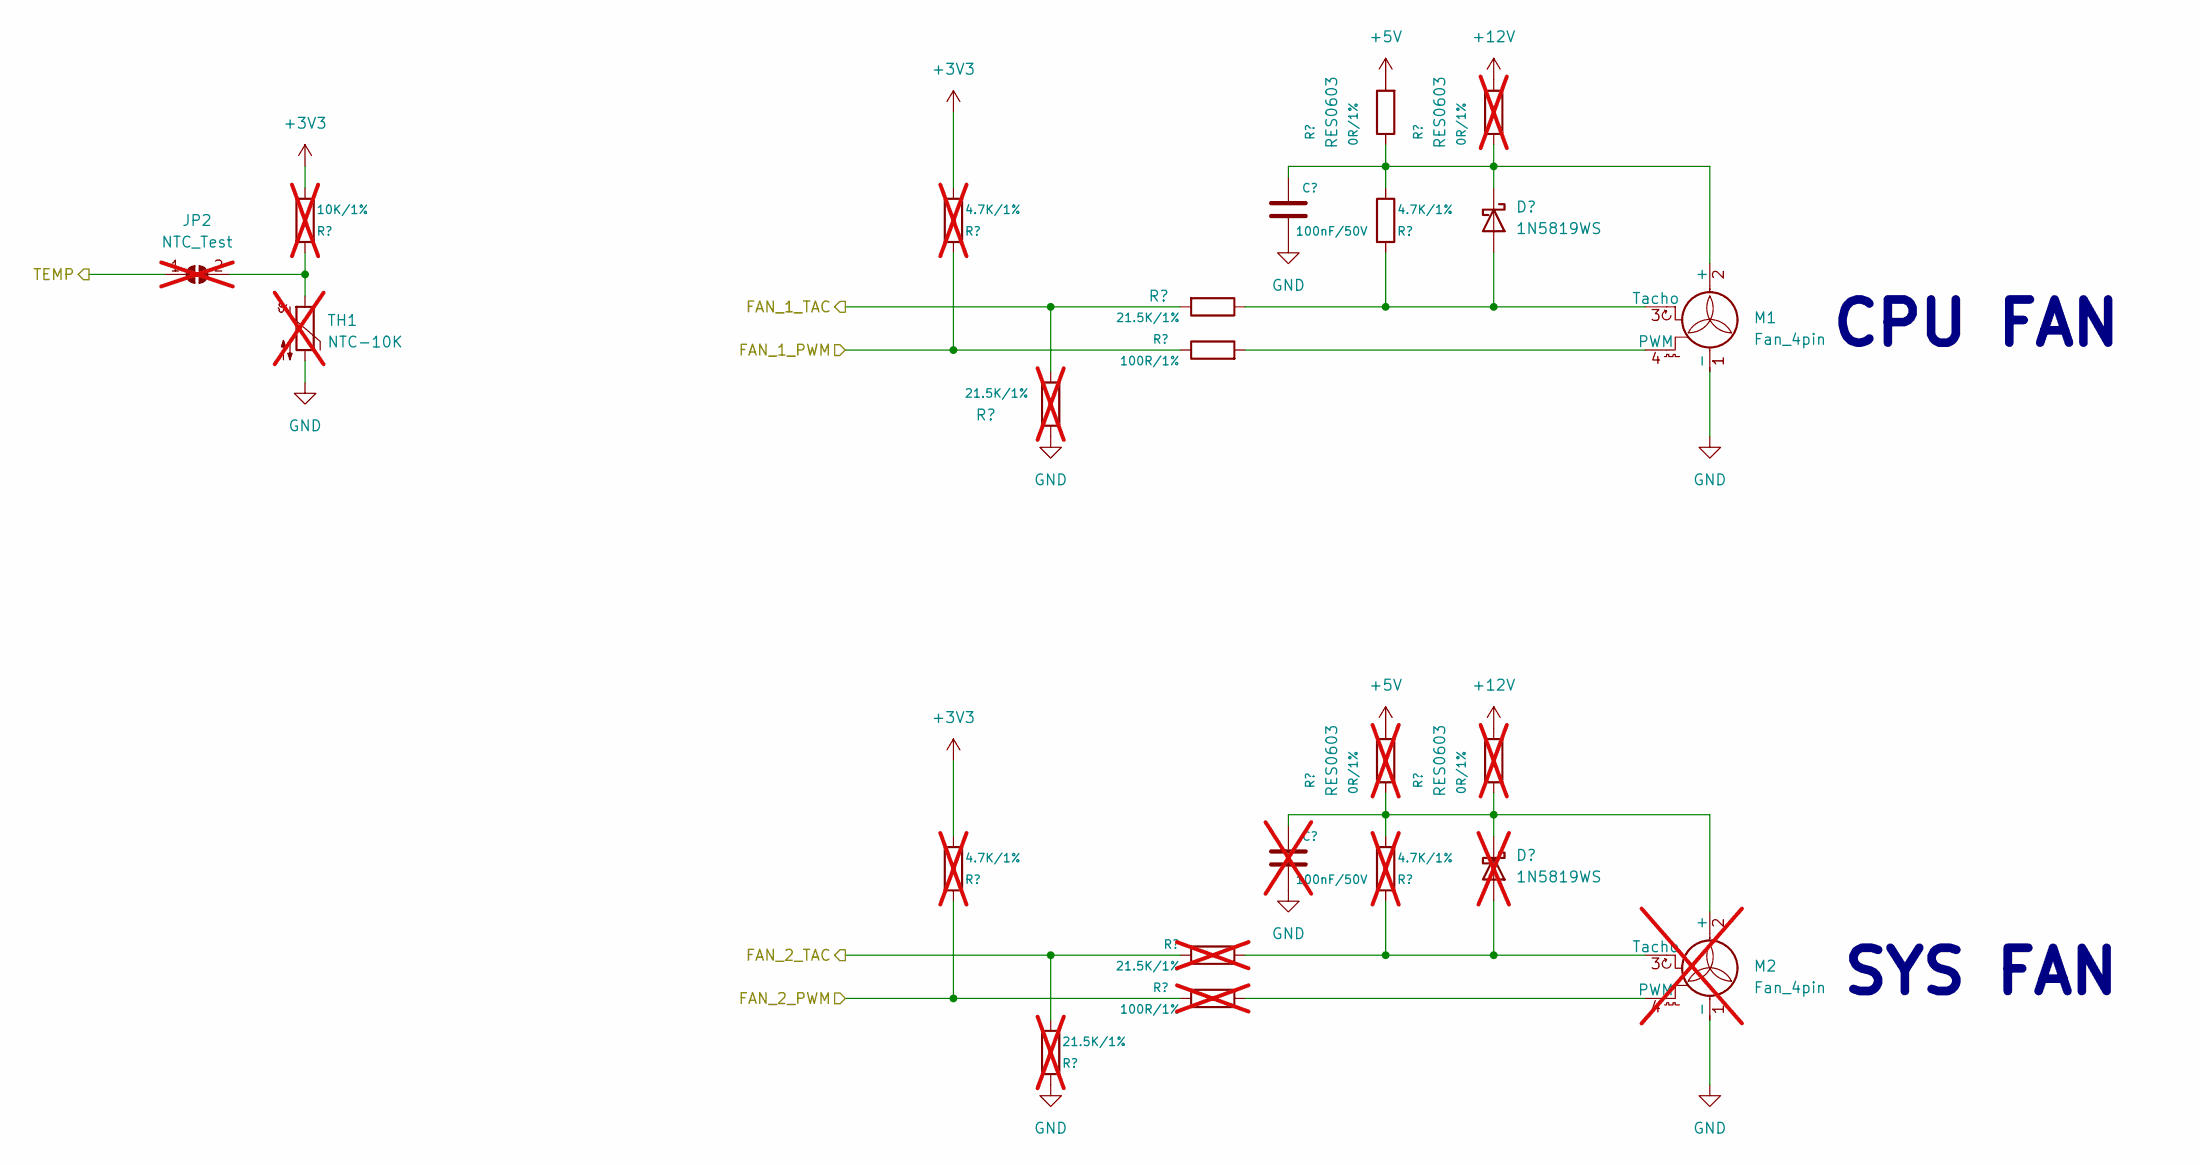
[picture p25: schematic fan&temp.kicad_sch]

Parts:
C74: 100nF/50V; C_0402_1005Metric
C75: 100nF/50V; C_0402_1005Metric; not fitted
D23: 1N5819WS; D_SOD-323
D24: 1N5819WS; D_SOD-323; not fitted
JP2: NTC_Test; SolderJumper-2_P1.3mm_Open_RoundedPad1.0x1.5mm; not fitted
M1: Fan_4pin; JST_PH_B4B-PH-K_1x04_P2.00mm_Vertical
M2: Fan_4pin; JST_PH_B4B-PH-K_1x04_P2.00mm_Vertical; not fitted
R1: 10K/1%; R_0402_1005Metric; not fitted
R10, R11, R37: 4.7K/1%; R_0402_1005Metric; not fitted
R17, R29, R32: 21.5K/1%; R_0402_1005Metric; not fitted
R30: 21.5K/1%; R_0402_1005Metric
R31: 100R/1%; R_0402_1005Metric
R33: 100R/1%; R_0402_1005Metric; not fitted
R34: 0R/1%; RES0603
R35: 4.7K/1%; R_0402_1005Metric
R36, R54, R55: 0R/1%; RES0603; not fitted
TH1: NTC-10K; R_0603_1608Metric; not fitted

Connections:
+3V3: R1.1, R10.1, R11.1
+5V: R34.2, R36.2
+12V: R54.2, R55.2
FAN_1_PWM: R10.2, R31.1
FAN_1_TAC: R17.1, R30.2
FAN_2_PWM: R11.2, R33.1
FAN_2_TAC: R29.1, R32.1
GND: C74.2, C75.2, M1.1 (-), M2.1 (-), R17.2, R29.2, TH1.2
unnamed: C74.1, D23.1 (K), M1.2 (+), R34.1, R35.1, R54.1
unnamed: C75.1, D24.1 (K), M2.2 (+), R36.1, R37.1, R55.1
unnamed: D23.2 (A), M1.3 (Tacho), R30.1, R35.2
unnamed: D24.2 (A), M2.3 (Tacho), R32.2, R37.2
unnamed: JP2.2 (B), R1.2, TH1.1
unnamed: M1.4 (PWM), R31.2
unnamed: M2.4 (PWM), R33.2
TEMP: JP2.1 (A)

Notes on the sheet:
CPU FAN
SYS FAN
