LtBrain/MuBook/hardware/v.1/fan_temp.kicad_sch

## KiCad design hardware/v.1/fan_temp.kicad_sch (2025-07-12)

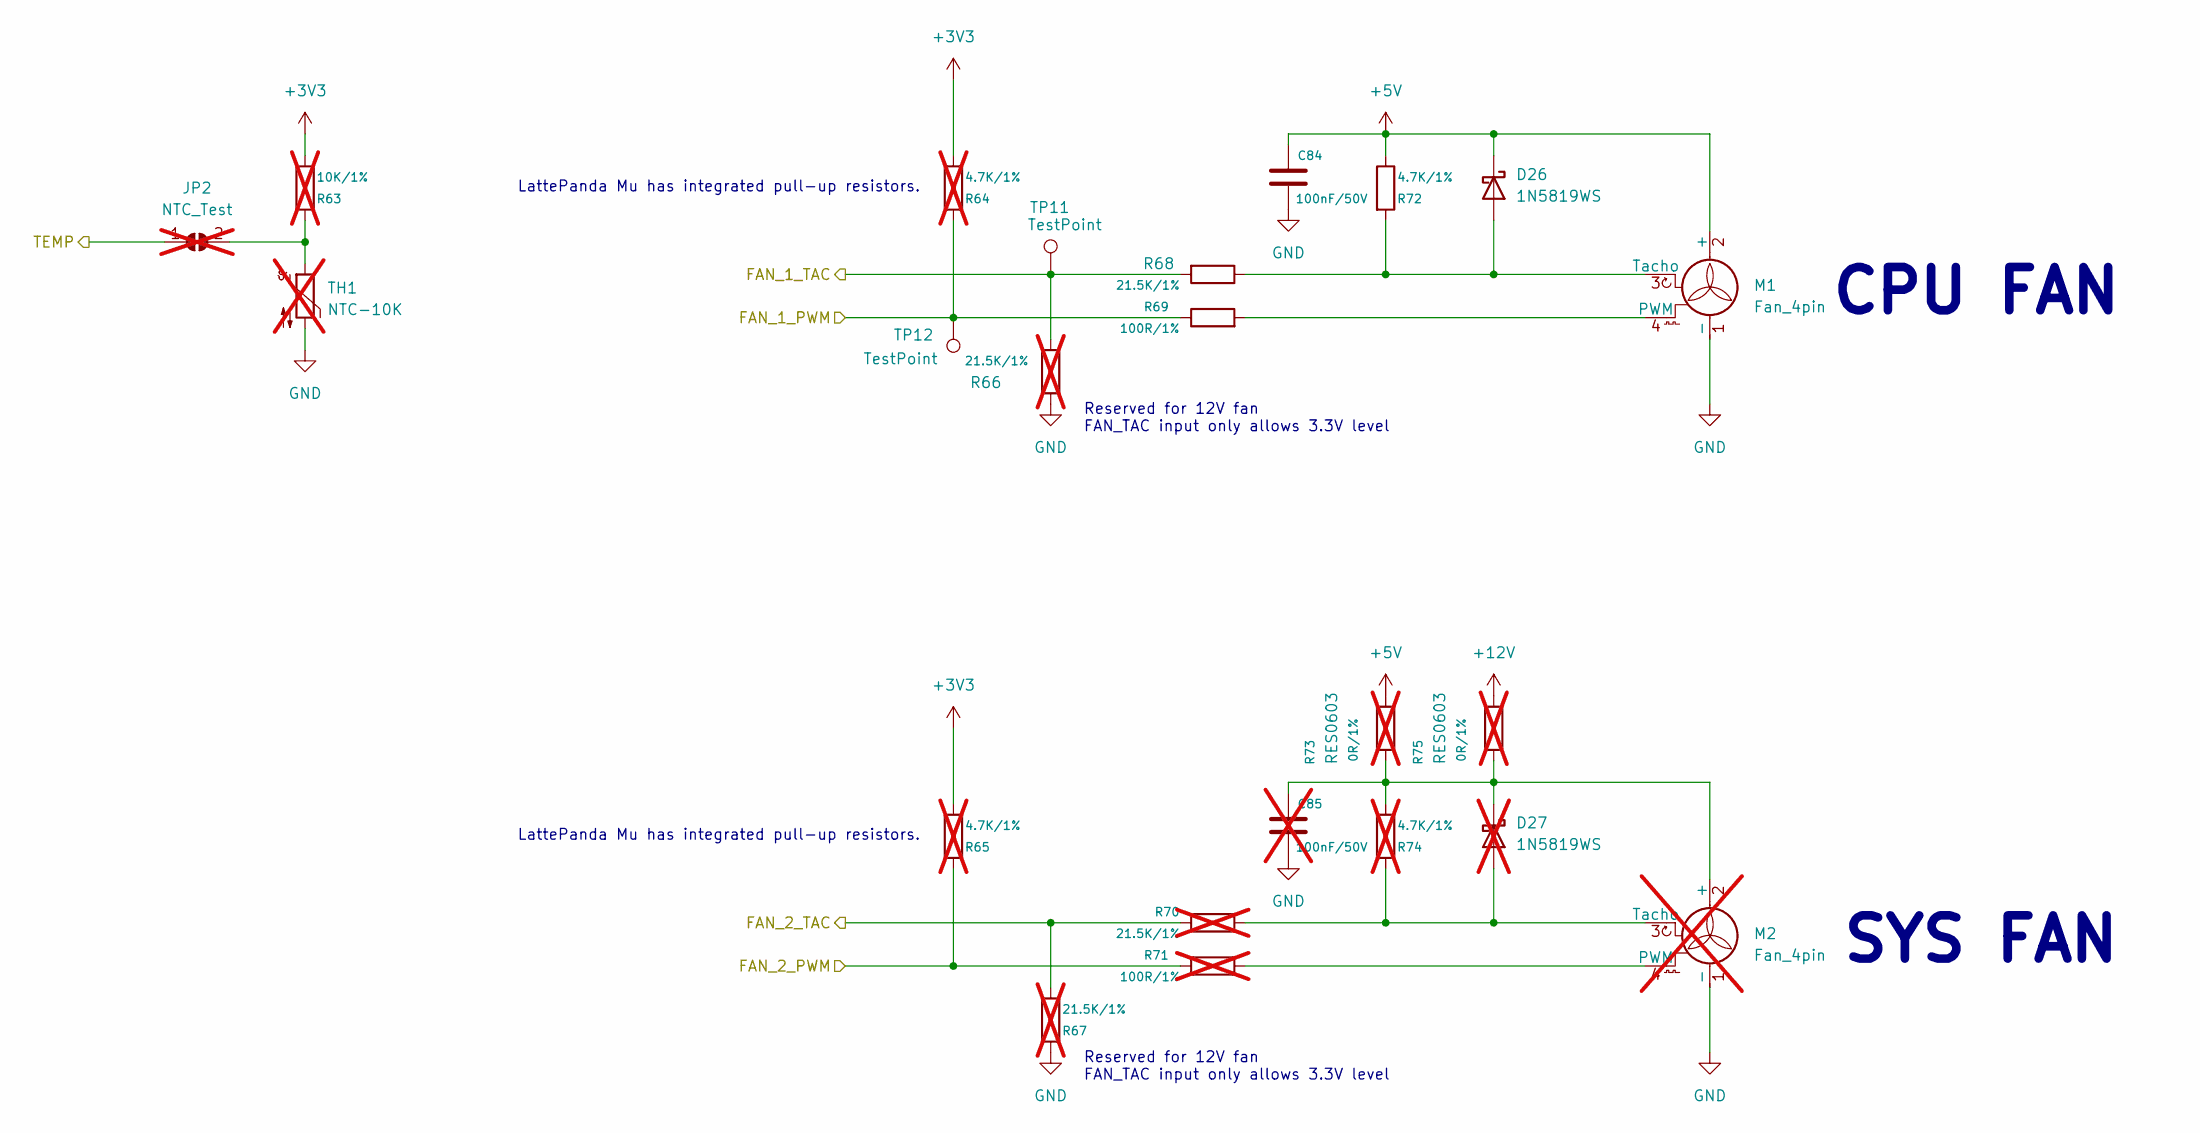
[picture p26: schematic fan_temp.kicad_sch]

Parts:
C84: 100nF/50V; C_0402_1005Metric
C85: 100nF/50V; C_0402_1005Metric; not fitted
D26: 1N5819WS; D_SOD-323
D27: 1N5819WS; D_SOD-323; not fitted
JP2: NTC_Test; SolderJumper-2_P1.3mm_Open_RoundedPad1.0x1.5mm; not fitted
M1: Fan_4pin; JST_PH_B4B-PH-K_1x04_P2.00mm_Vertical
M2: Fan_4pin; JST_PH_B4B-PH-K_1x04_P2.00mm_Vertical; not fitted
R63: 10K/1%; R_0402_1005Metric; not fitted
R64, R65, R74: 4.7K/1%; R_0402_1005Metric; not fitted
R66, R67, R70: 21.5K/1%; R_0402_1005Metric; not fitted
R68: 21.5K/1%; R_0402_1005Metric
R69: 100R/1%; R_0402_1005Metric
R71: 100R/1%; R_0402_1005Metric; not fitted
R72: 4.7K/1%; R_0402_1005Metric
R73, R75: 0R/1%; RES0603; not fitted
TH1: NTC-10K; R_0603_1608Metric; not fitted
TP11, TP12: TestPoint; TestPoint_Pad_D1.5mm

Connections:
+3V3: R63.1, R64.1, R65.1
+5V: C84.1, D26.1 (K), M1.2 (+), R72.1, R73.2
+12V: R75.2
FAN_1_PWM: R64.2, R69.1, TP12.1
FAN_1_TAC: R66.1, R68.2, TP11.1
FAN_2_PWM: R65.2, R71.1
FAN_2_TAC: R67.1, R70.1
GND: C84.2, C85.2, M1.1 (-), M2.1 (-), R66.2, R67.2, TH1.2
unnamed: C85.1, D27.1 (K), M2.2 (+), R73.1, R74.1, R75.1
unnamed: D26.2 (A), M1.3 (Tacho), R68.1, R72.2
unnamed: D27.2 (A), M2.3 (Tacho), R70.2, R74.2
unnamed: JP2.2 (B), R63.2, TH1.1
unnamed: M1.4 (PWM), R69.2
unnamed: M2.4 (PWM), R71.2
TEMP: JP2.1 (A)

Notes on the sheet:
CPU FAN
SYS FAN
Reserved for 12V fan FAN_TAC input only allows 3.3V level
LattePanda Mu has integrated pull-up resistors.
